henryhsun/TuxTester/04 - Media/Photos & Videos/02 - Progress Documentation/electrical_debug (1).JPG

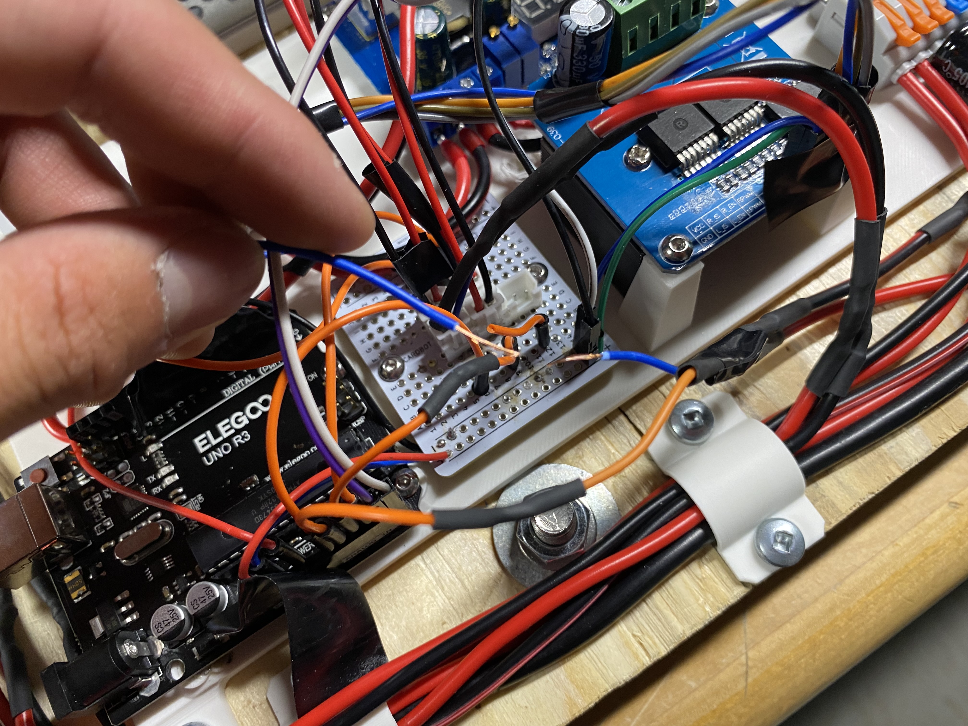
04 - Media/Photos & Videos/02 - Progress Documentation/electrical_debug (1).JPG
