henryhsun/TuxTester/02 - Electrical/Logic_Diagram.png

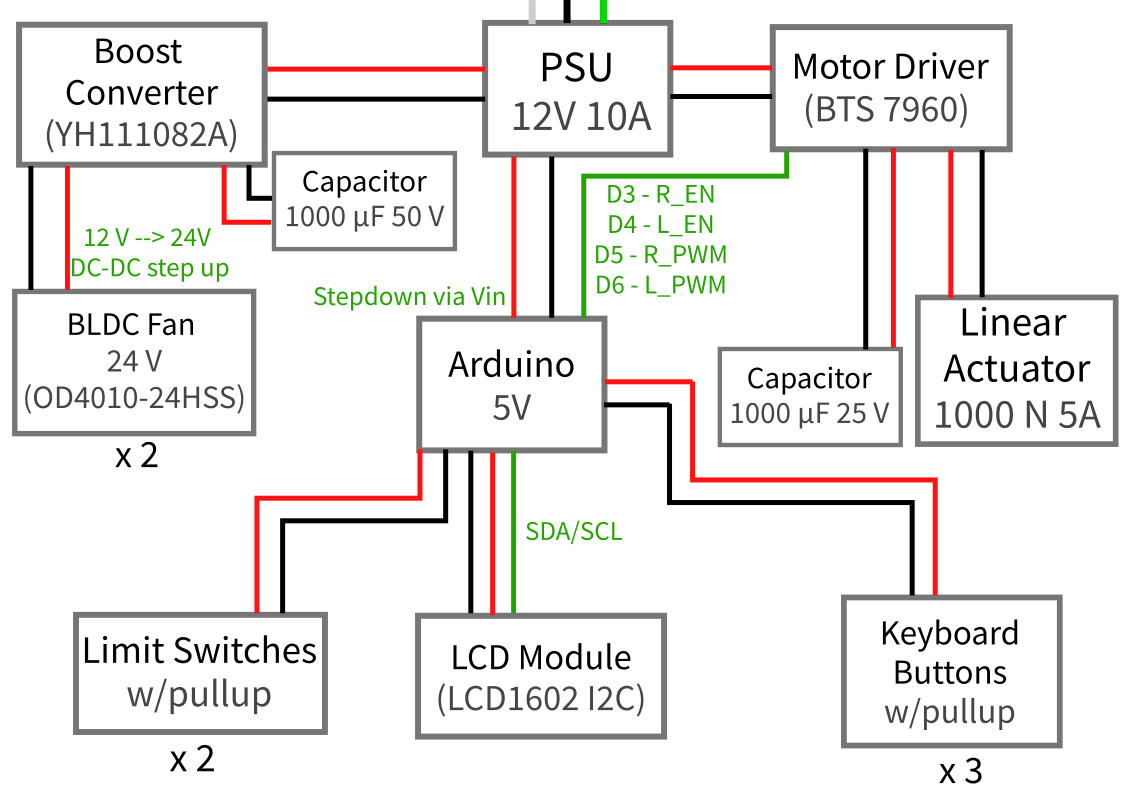
02 - Electrical/Logic_Diagram.png
