henryhsun/TuxTester/02 - Electrical/Schematic Screenshot.png

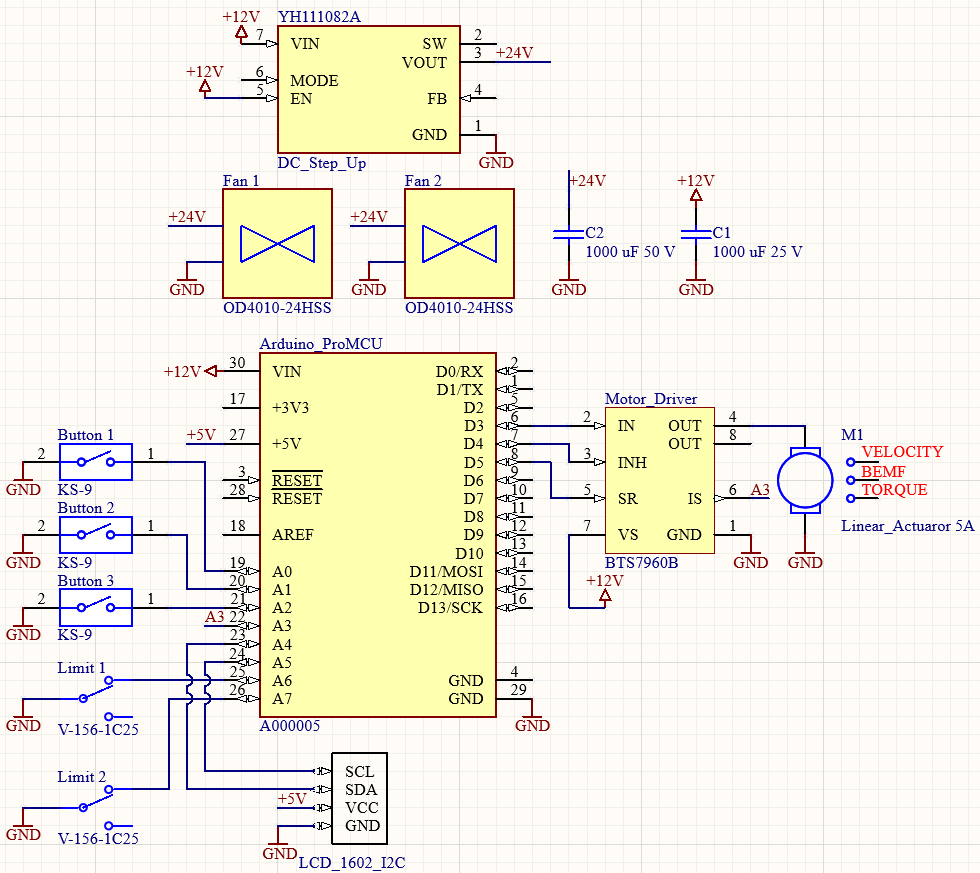
02 - Electrical/Schematic Screenshot.png
