henryhsun/TuxTester/03 - Software/program_flowchart.png

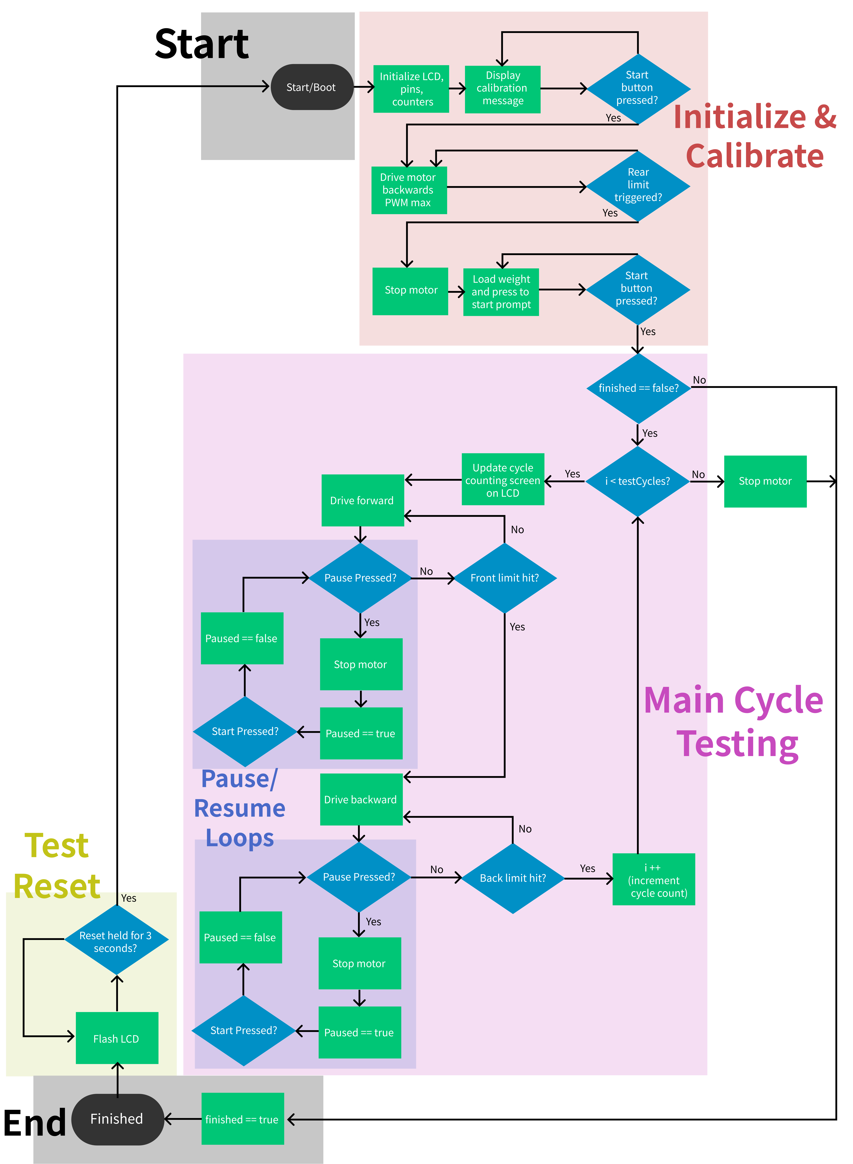
03 - Software/program_flowchart.png
