henryhsun/TuxTester/04 - Media/Photos & Videos/02 - Progress Documentation/CI (5).JPG

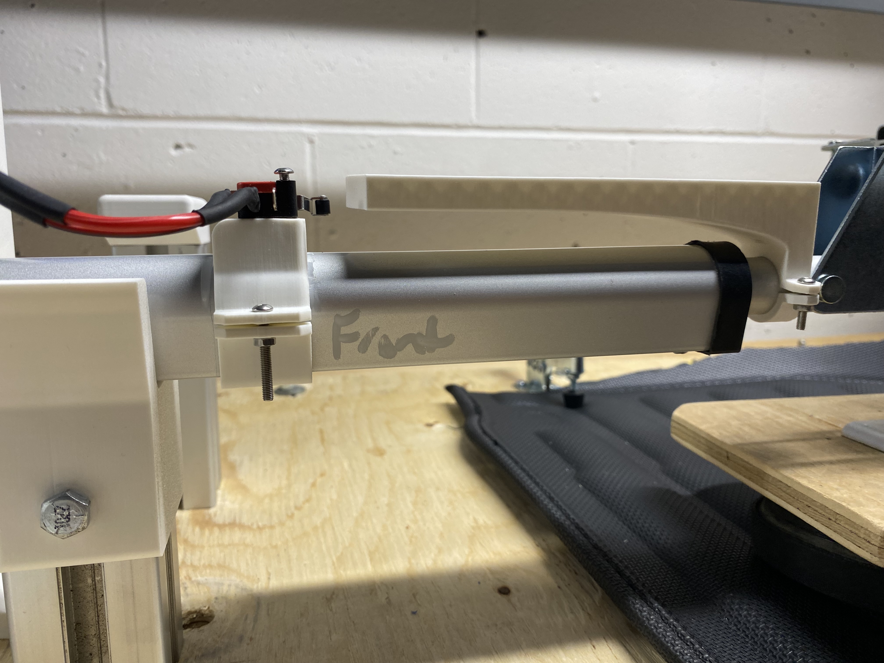
04 - Media/Photos & Videos/02 - Progress Documentation/CI (5).JPG
