henryhsun/TuxTester/04 - Media/Photos & Videos/02 - Progress Documentation/general (8).JPG

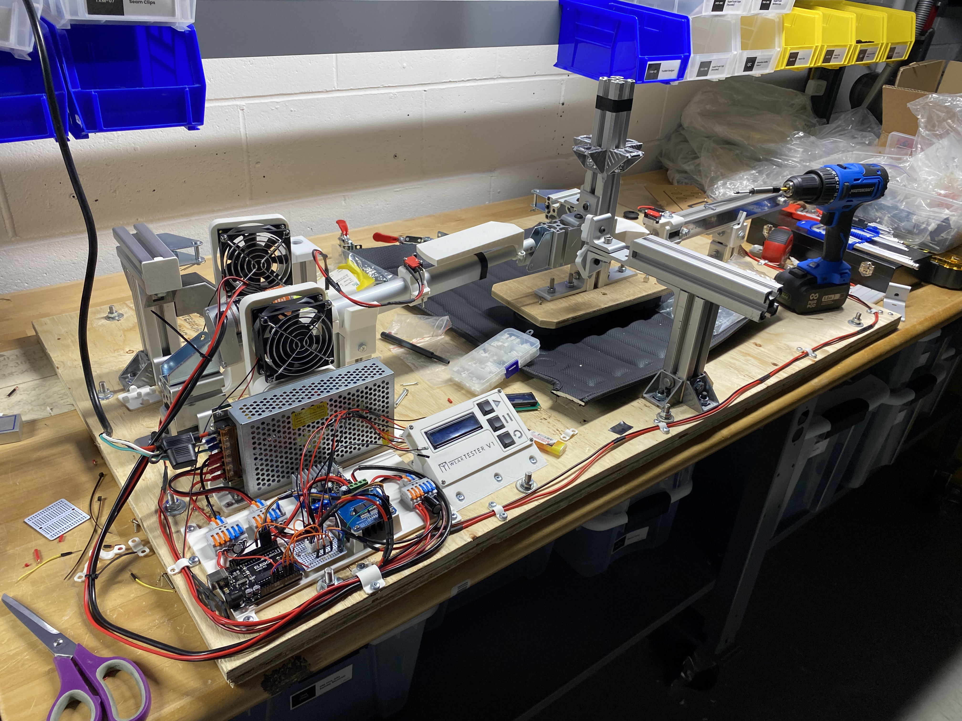
04 - Media/Photos & Videos/02 - Progress Documentation/general (8).JPG
