henryhsun/TuxTester/04 - Media/Photos & Videos/02 - Progress Documentation/limit_switch.JPG

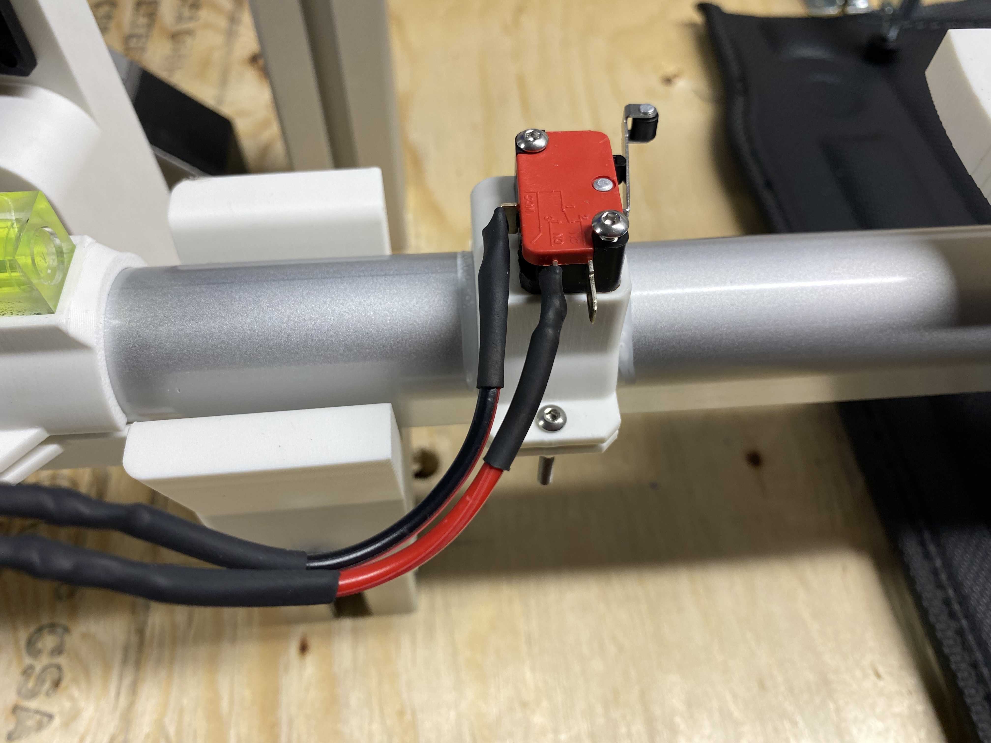
04 - Media/Photos & Videos/02 - Progress Documentation/limit_switch.JPG
