henryhsun/TuxTester/04 - Media/Photos & Videos/02 - Progress Documentation/magnet_holder (1).JPG

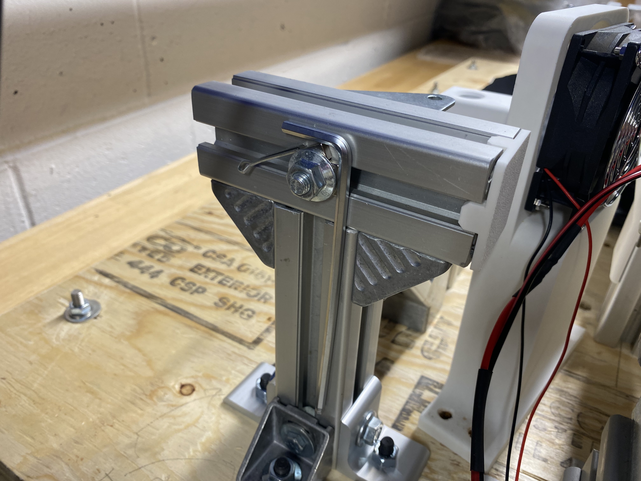
04 - Media/Photos & Videos/02 - Progress Documentation/magnet_holder (1).JPG
