henryhsun/TuxTester/04 - Media/Photos & Videos/03 - Misc/blown_cap.JPG

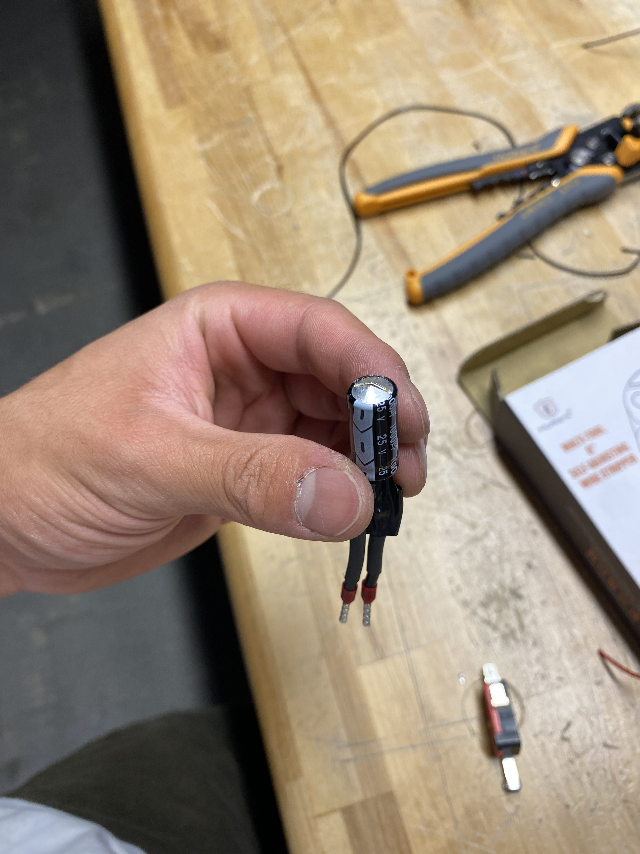
04 - Media/Photos & Videos/03 - Misc/blown_cap.JPG
