henryhsun/TuxTester/04 - Media/Photos & Videos/03 - Misc/broken_snips.JPG

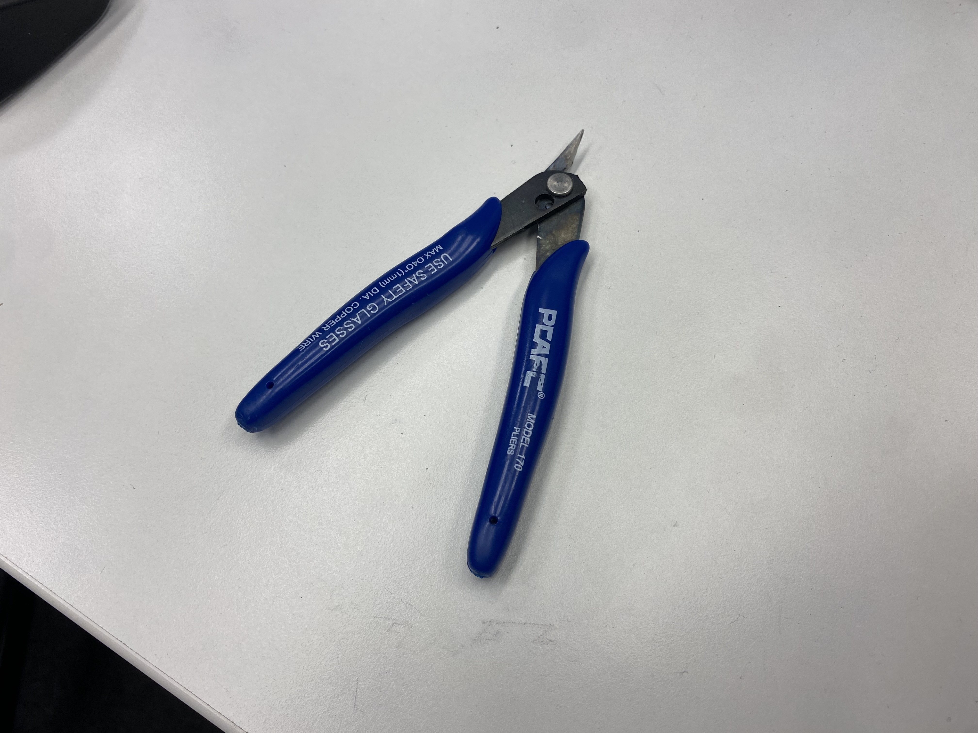
04 - Media/Photos & Videos/03 - Misc/broken_snips.JPG
