henryhsun/TuxTester/04 - Media/Photos & Videos/03 - Misc/cooked_LCD (1).JPG

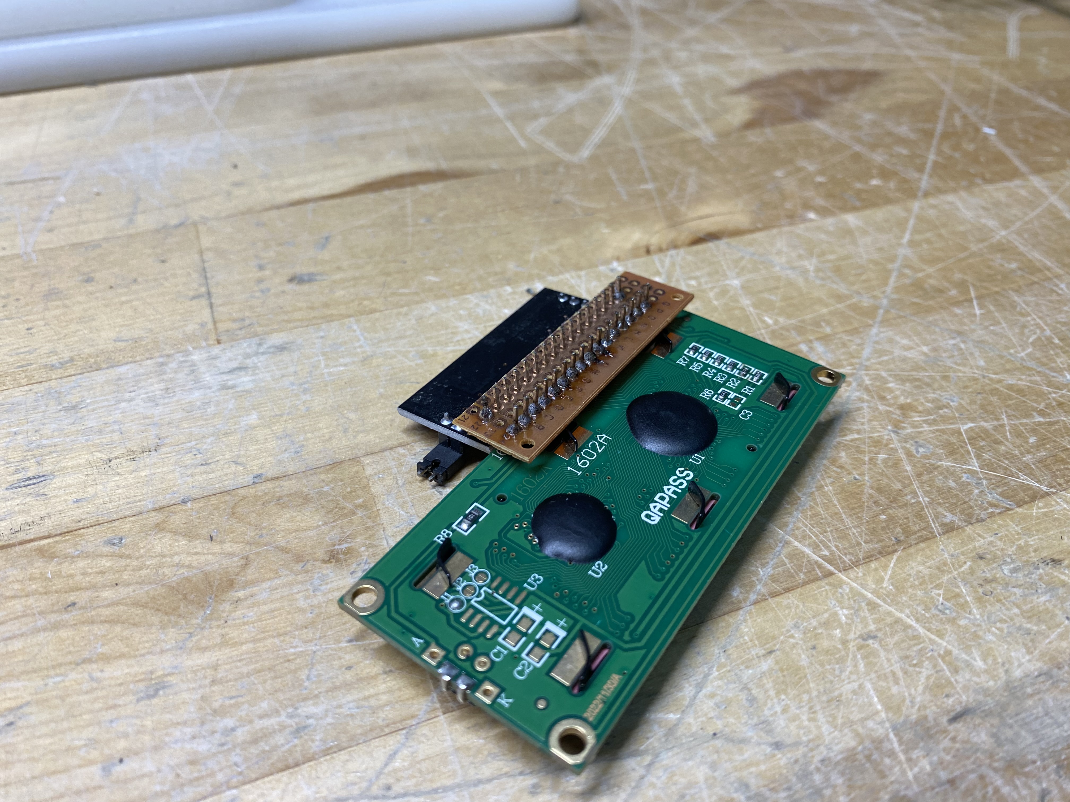
04 - Media/Photos & Videos/03 - Misc/cooked_LCD (1).JPG
