henryhsun/TuxTester/04 - Media/Photos & Videos/03 - Misc/erm/Thread Spray (7).JPG

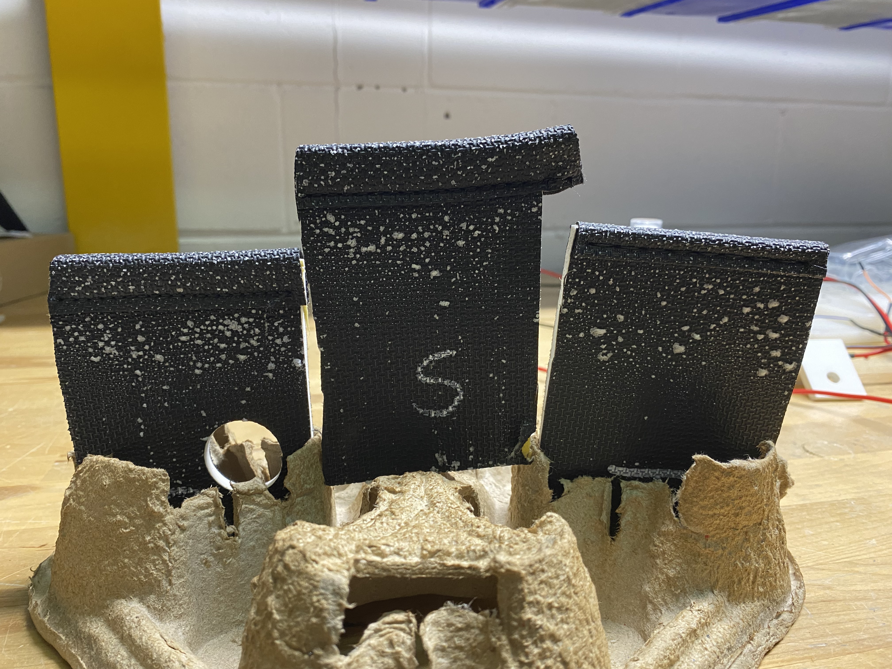
04 - Media/Photos & Videos/03 - Misc/erm/Thread Spray (7).JPG
