henryhsun/TuxTester/04 - Media/Photos & Videos/03 - Misc/erm/Thread Wick (4).JPG

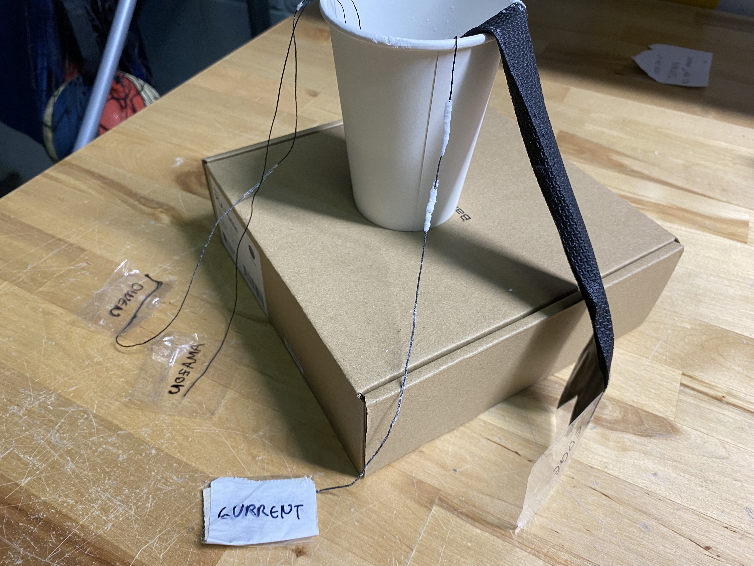
04 - Media/Photos & Videos/03 - Misc/erm/Thread Wick (4).JPG
