henryhsun/TuxTester/04 - Media/Photos & Videos/03 - Misc/erm/Trunk Study (3).JPG

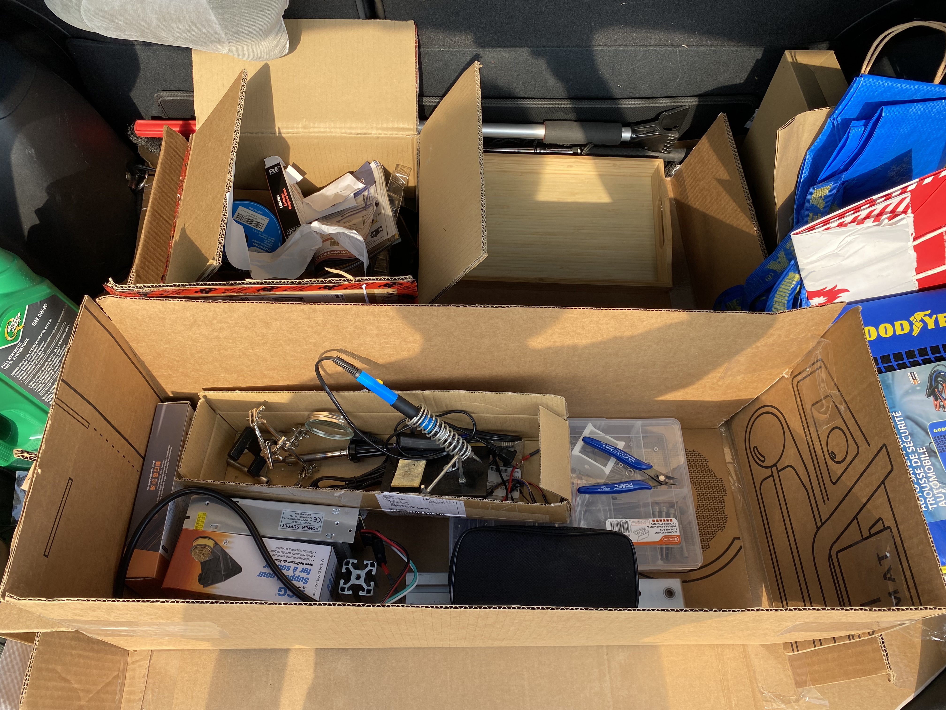
04 - Media/Photos & Videos/03 - Misc/erm/Trunk Study (3).JPG
