henryhsun/TuxTester/01 - Mechanical/CAD/V4 Release 1/Final1Final1PSU_assembly.SLDASM

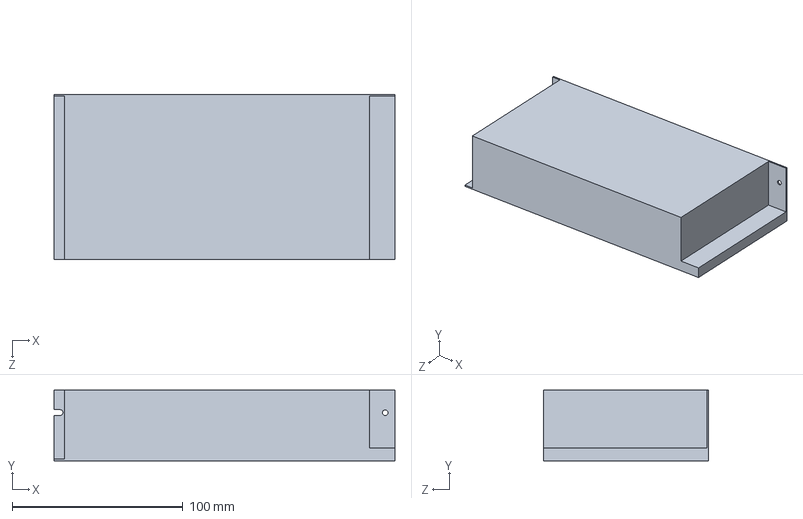
[picture p54: CAD file, 2026-01-19]
01 - Mechanical/CAD/V4 Release 1/Final1Final1PSU_assembly.SLDASM
200.0 x 41.5 x 97.0 mm
