henryhsun/TuxTester/01 - Mechanical/CAD/V3..5 Revised 3D Prints and assembly/STEP/master_extrusion connector.STEP

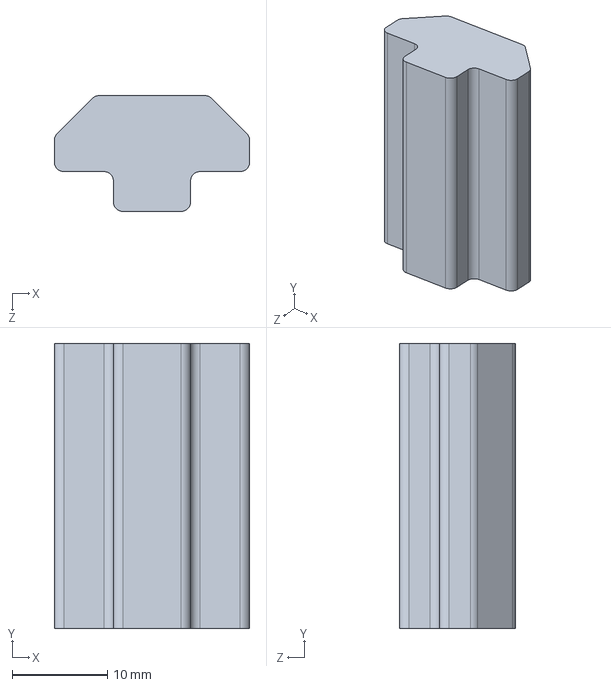
[picture p68: CAD file, 2025-09-29]
01 - Mechanical/CAD/V3..5 Revised 3D Prints and assembly/STEP/master_extrusion connector.STEP
20.6 x 30.0 x 12.2 mm
