henryhsun/TuxTester/01 - Mechanical/CAD/V4 Release 1/Final1masterLevel.SLDPRT

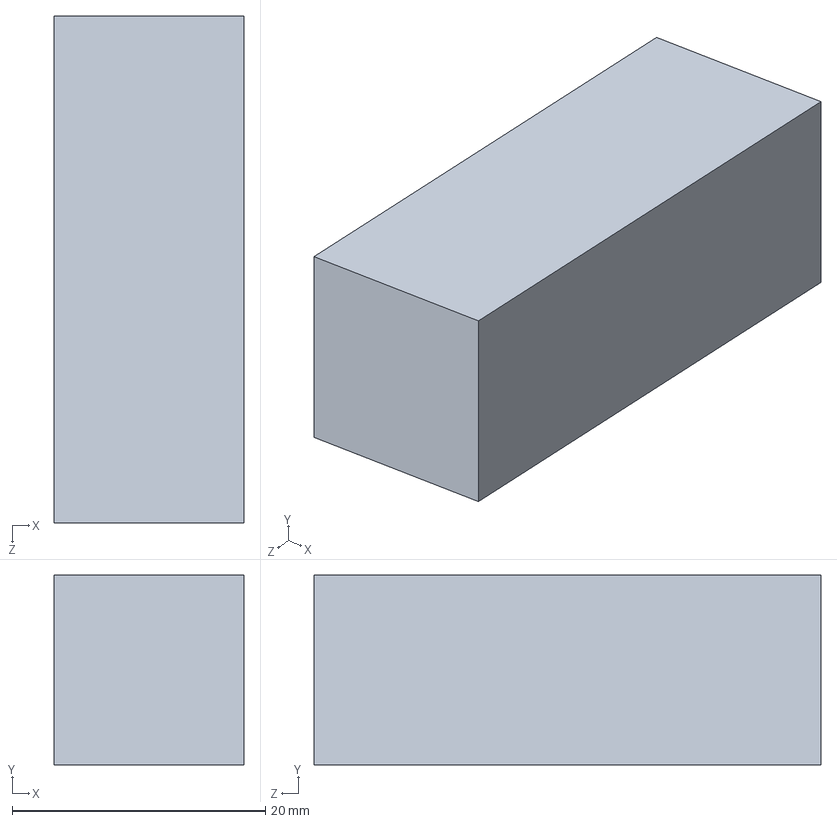
[picture p69: CAD file, 2026-01-19]
01 - Mechanical/CAD/V4 Release 1/Final1masterLevel.SLDPRT
15.0 x 15.0 x 40.0 mm
