henryhsun/TuxTester/01 - Mechanical/CAD/V3..5 Revised 3D Prints and assembly/STEP/master_Hinge_Bushing3.STEP

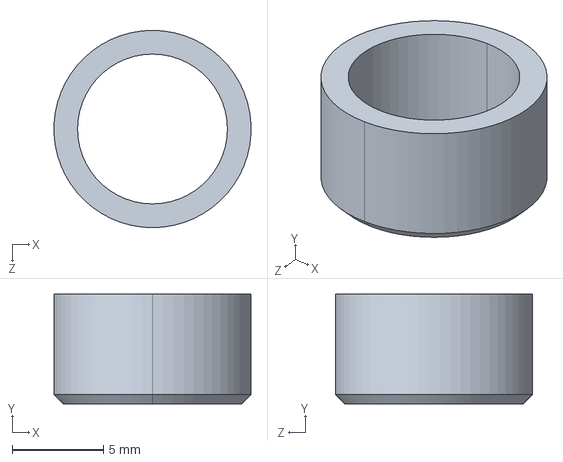
[picture p70: CAD file, 2025-09-29]
01 - Mechanical/CAD/V3..5 Revised 3D Prints and assembly/STEP/master_Hinge_Bushing3.STEP
10.8 x 6.00 x 10.8 mm
