henryhsun/TuxTester/01 - Mechanical/CAD/V3..5 Revised 3D Prints and assembly/STEP/master_Sole Spacer.STEP

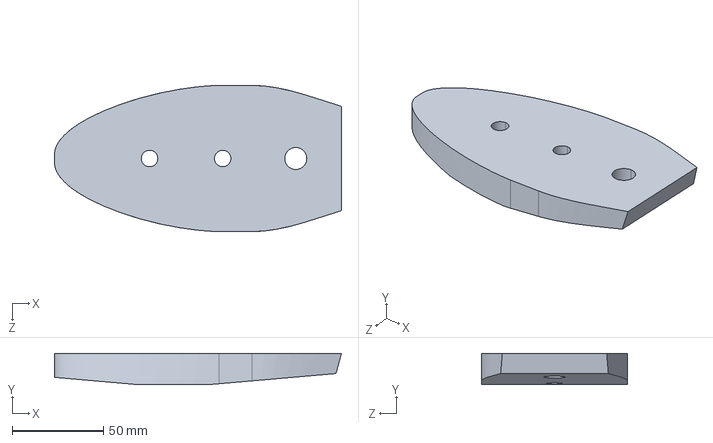
[picture p71: CAD file, 2025-09-29]
01 - Mechanical/CAD/V3..5 Revised 3D Prints and assembly/STEP/master_Sole Spacer.STEP
157.0 x 17.0 x 80.0 mm
