henryhsun/TuxTester/01 - Mechanical/CAD/V4 Release 1/Final1masterRuler.SLDPRT

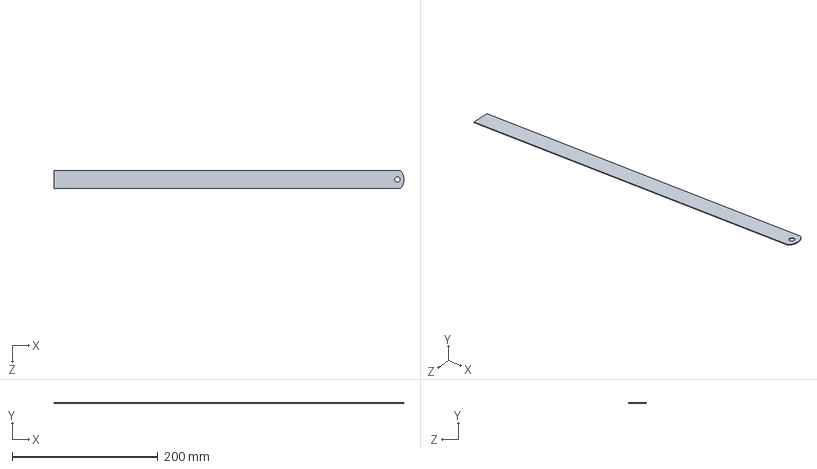
[picture p72: CAD file, 2026-01-19]
01 - Mechanical/CAD/V4 Release 1/Final1masterRuler.SLDPRT
479.9 x 0.9 x 25.1 mm
