henryhsun/TuxTester/01 - Mechanical/CAD/V3..5 Revised 3D Prints and assembly/STEP/master_rulerPointer.STEP

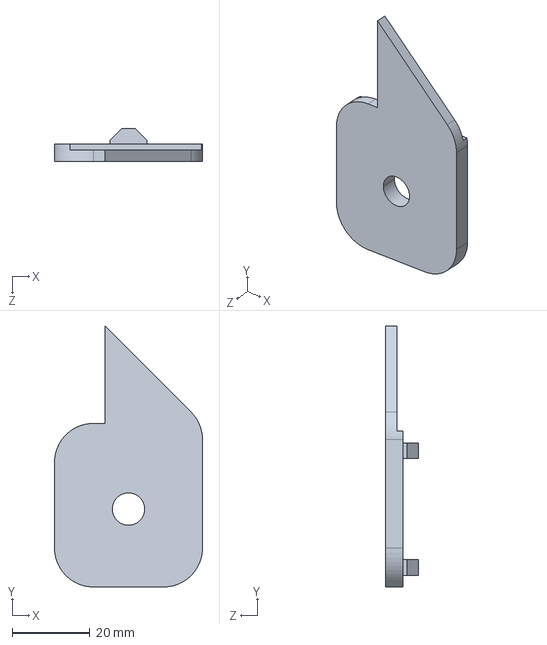
[picture p73: CAD file, 2025-09-29]
01 - Mechanical/CAD/V3..5 Revised 3D Prints and assembly/STEP/master_rulerPointer.STEP
38.0 x 67.0 x 8.50 mm
