henryhsun/TuxTester/01 - Mechanical/CAD/V3..5 Revised 3D Prints and assembly/STEP/masterSwitch_Mount.STEP

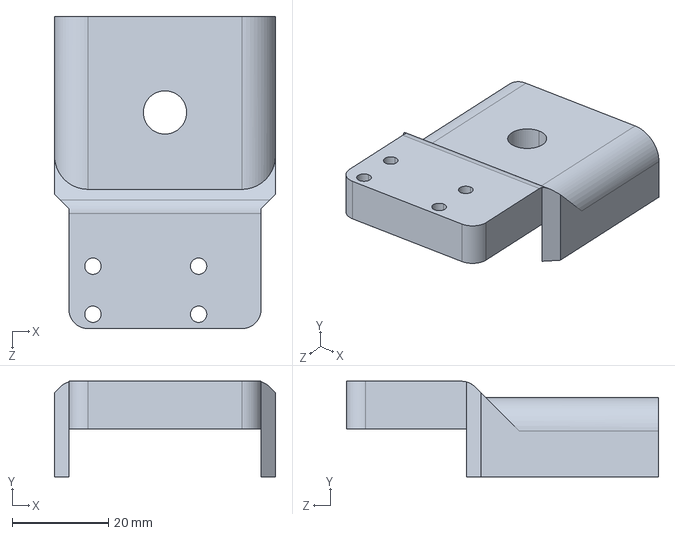
[picture p75: CAD file, 2025-09-29]
01 - Mechanical/CAD/V3..5 Revised 3D Prints and assembly/STEP/masterSwitch_Mount.STEP
46.0 x 19.9 x 65.0 mm
