henryhsun/TuxTester/01 - Mechanical/CAD/V3..5 Revised 3D Prints and assembly/STEP/master_Hinge_Spacer.STEP

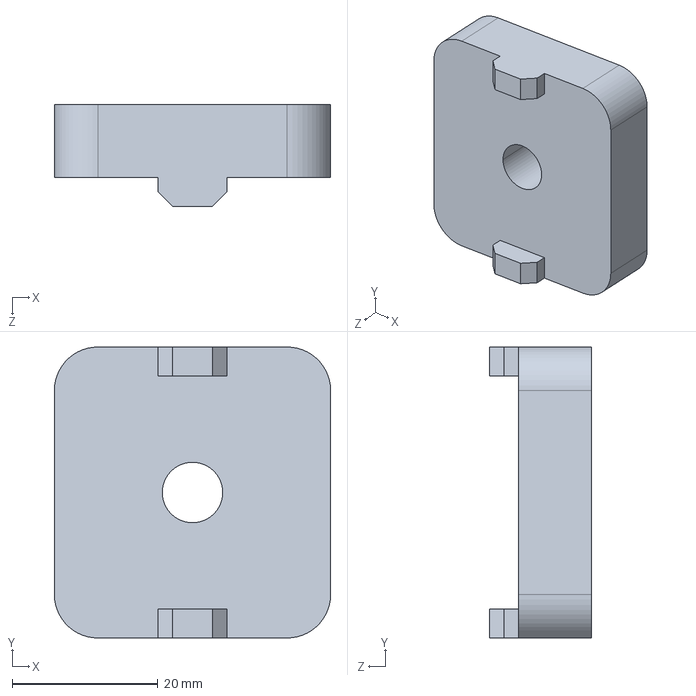
[picture p77: CAD file, 2025-09-29]
01 - Mechanical/CAD/V3..5 Revised 3D Prints and assembly/STEP/master_Hinge_Spacer.STEP
38.0 x 40.0 x 14.0 mm
