henryhsun/TuxTester/01 - Mechanical/CAD/V4 Release 1/Final1masterRivet - long.SLDPRT

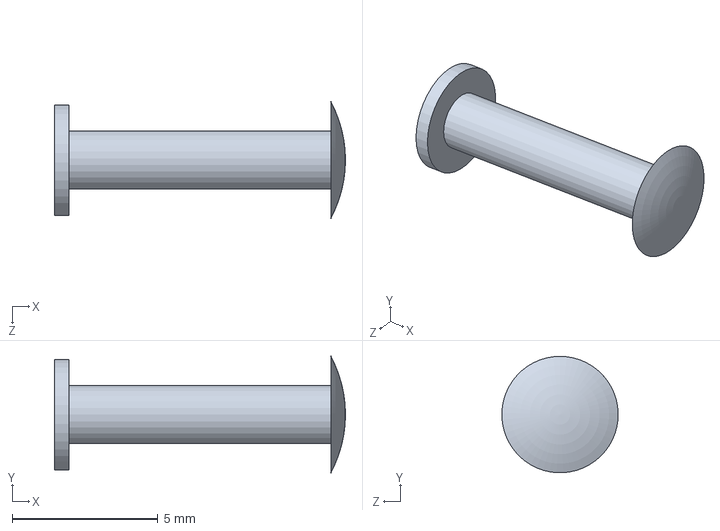
[picture p78: CAD file, 2026-01-19]
01 - Mechanical/CAD/V4 Release 1/Final1masterRivet - long.SLDPRT
10.0 x 4.00 x 4.00 mm
