henryhsun/TuxTester/01 - Mechanical/CAD/V3..5 Revised 3D Prints and assembly/STEP/masterSwitch_Actuator_Mount.STEP

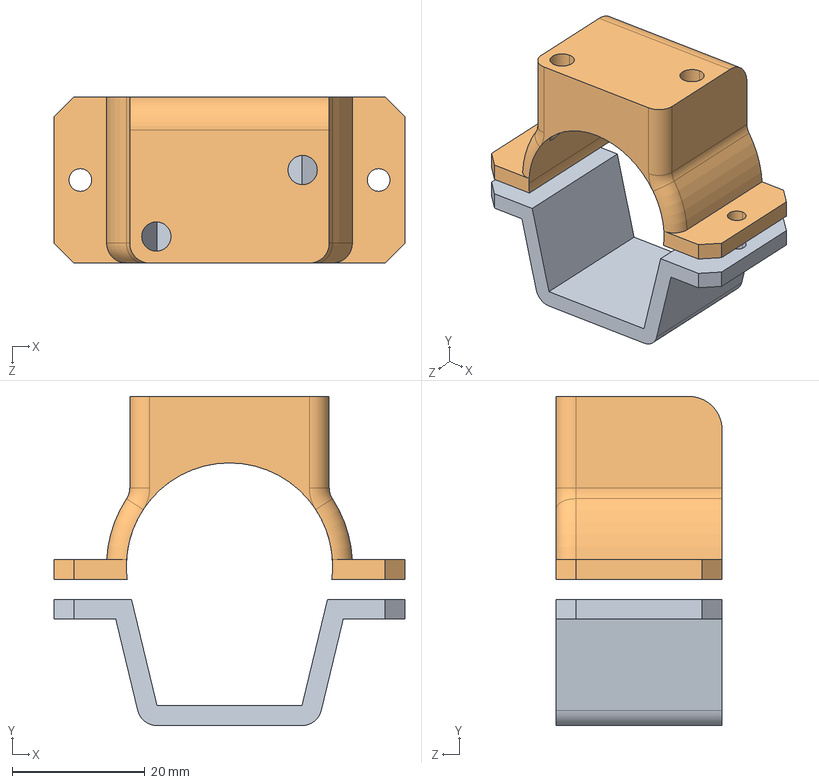
[picture p79: CAD file, 2025-09-29]
01 - Mechanical/CAD/V3..5 Revised 3D Prints and assembly/STEP/masterSwitch_Actuator_Mount.STEP
52.8 x 49.5 x 25.0 mm
