henryhsun/TuxTester/01 - Mechanical/CAD/V3..5 Revised 3D Prints and assembly/STEP/master_actuatorHolder1.STEP

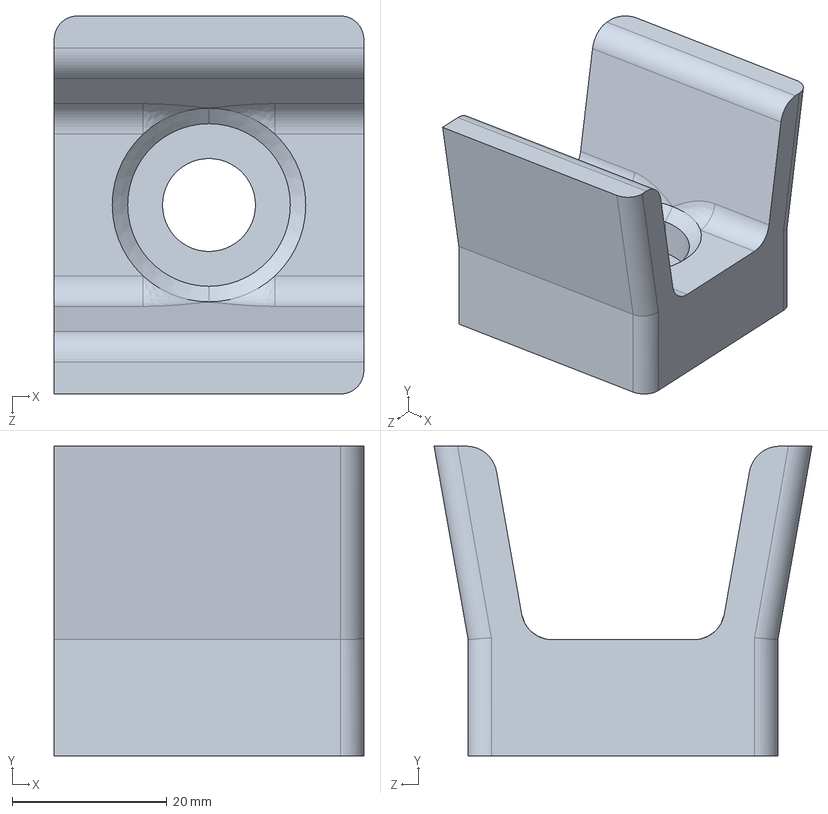
[picture p80: CAD file, 2025-09-29]
01 - Mechanical/CAD/V3..5 Revised 3D Prints and assembly/STEP/master_actuatorHolder1.STEP
40.0 x 40.0 x 48.8 mm
