henryhsun/TuxTester/01 - Mechanical/CAD/V4 Release 1/Final1masterShaft_Clamp_Striker.SLDPRT

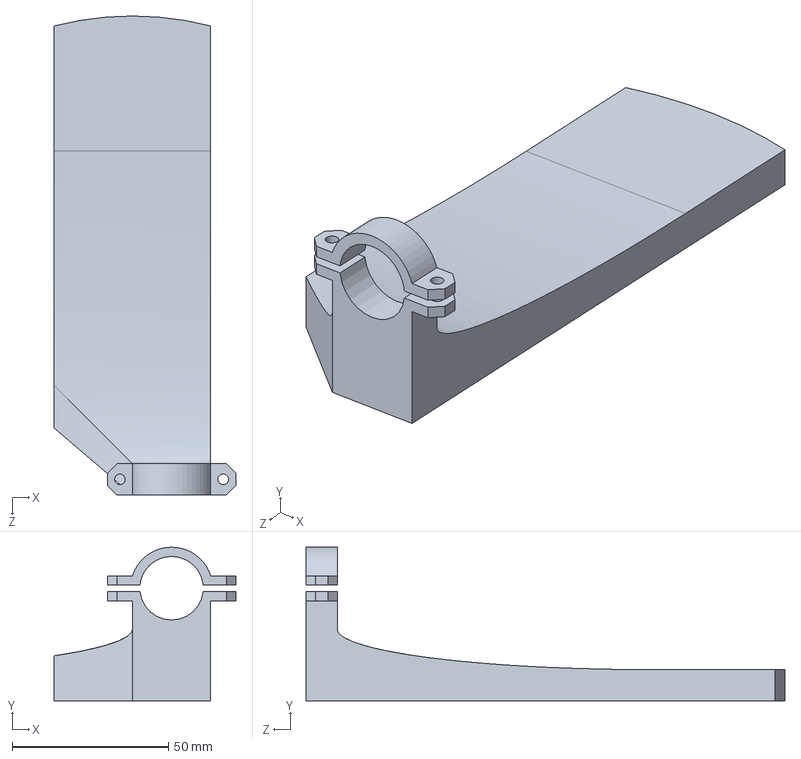
[picture p81: CAD file, 2026-01-19]
01 - Mechanical/CAD/V4 Release 1/Final1masterShaft_Clamp_Striker.SLDPRT
58.1 x 49.1 x 153.2 mm
