henryhsun/TuxTester/01 - Mechanical/CAD/V4 Release 1/Final1masterArm.SLDPRT

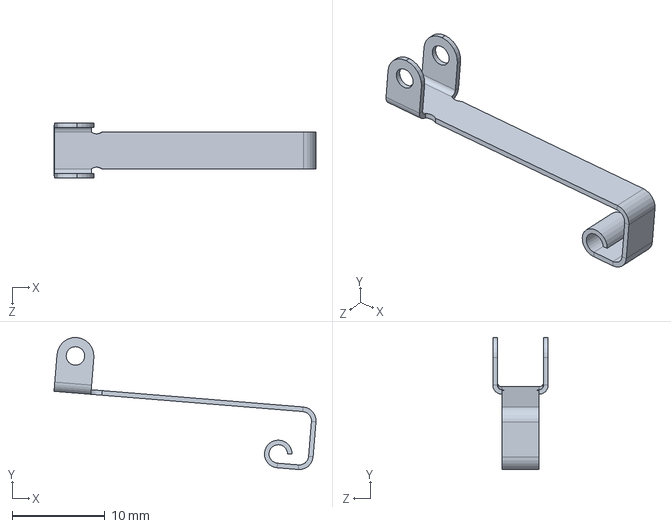
[picture p82: CAD file, 2026-01-19]
01 - Mechanical/CAD/V4 Release 1/Final1masterArm.SLDPRT
28.3 x 14.3 x 6.00 mm
