henryhsun/TuxTester/01 - Mechanical/CAD/V4 Release 1/Final1masterActuator_Body.SLDPRT

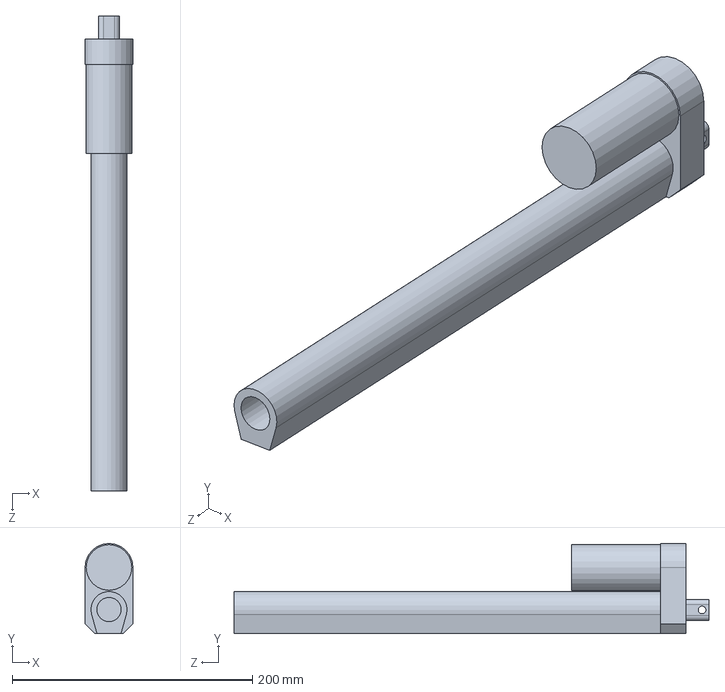
[picture p83: CAD file, 2026-01-19]
01 - Mechanical/CAD/V4 Release 1/Final1masterActuator_Body.SLDPRT
40.0 x 75.0 x 395.2 mm
