henryhsun/TuxTester/01 - Mechanical/CAD/V4 Release 1/Final1master4040_2HoleBracket.SLDPRT

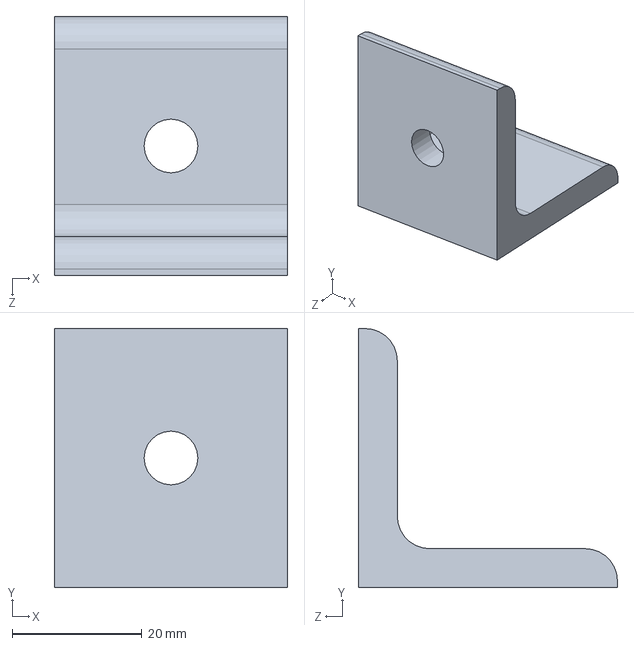
[picture p85: CAD file, 2026-01-19]
01 - Mechanical/CAD/V4 Release 1/Final1master4040_2HoleBracket.SLDPRT
36.0 x 40.0 x 40.0 mm
