henryhsun/TuxTester/01 - Mechanical/CAD/V4 Release 1/Final1Final1fan holderSHORT.SLDPRT

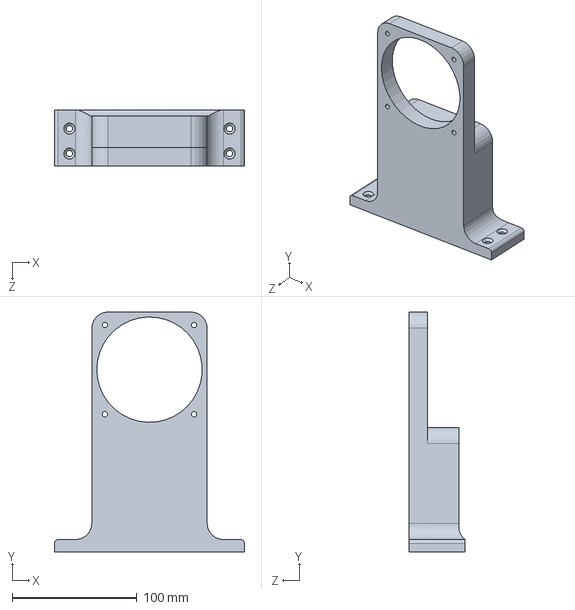
[picture p86: CAD file, 2026-01-19]
01 - Mechanical/CAD/V4 Release 1/Final1Final1fan holderSHORT.SLDPRT
152.5 x 192.5 x 45.0 mm
