henryhsun/TuxTester/01 - Mechanical/CAD/V4 Release 1/Final1masterBody.SLDPRT

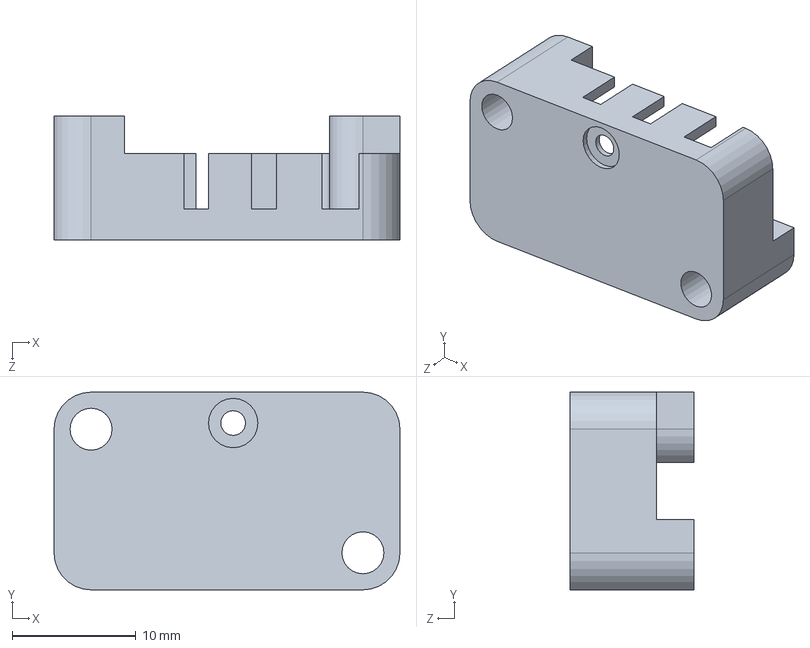
[picture p87: CAD file, 2026-01-19]
01 - Mechanical/CAD/V4 Release 1/Final1masterBody.SLDPRT
28.0 x 16.0 x 10.0 mm
