henryhsun/TuxTester/01 - Mechanical/CAD/V4 Release 1/Final1masterActuator_Shaft.SLDPRT

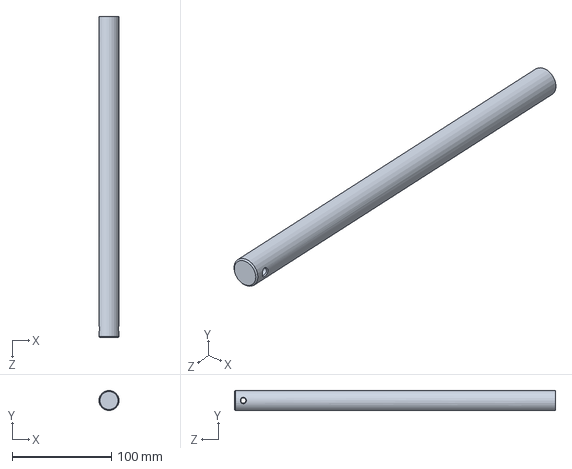
[picture p88: CAD file, 2026-01-19]
01 - Mechanical/CAD/V4 Release 1/Final1masterActuator_Shaft.SLDPRT
20.2 x 20.2 x 323.3 mm
