henryhsun/TuxTester/01 - Mechanical/CAD/V4 Release 1/Final1master4040 x 45.4.SLDPRT

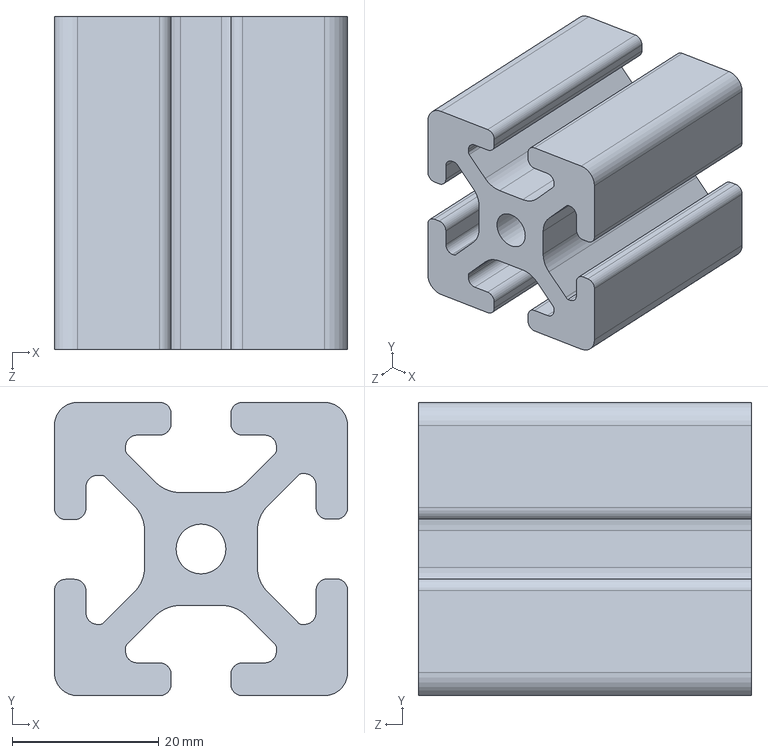
[picture p89: CAD file, 2026-01-19]
01 - Mechanical/CAD/V4 Release 1/Final1master4040 x 45.4.SLDPRT
40.0 x 40.0 x 45.4 mm
