henryhsun/TuxTester/01 - Mechanical/CAD/V4 Release 1/Final1masterActuator_Pin.SLDPRT

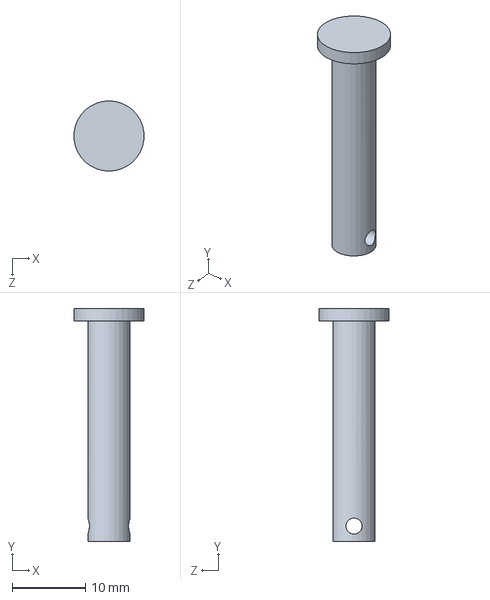
[picture p90: CAD file, 2026-01-19]
01 - Mechanical/CAD/V4 Release 1/Final1masterActuator_Pin.SLDPRT
9.56 x 31.9 x 9.60 mm
