henryhsun/TuxTester/01 - Mechanical/CAD/V4 Release 1/Final1masterSwitch_Mount.SLDPRT

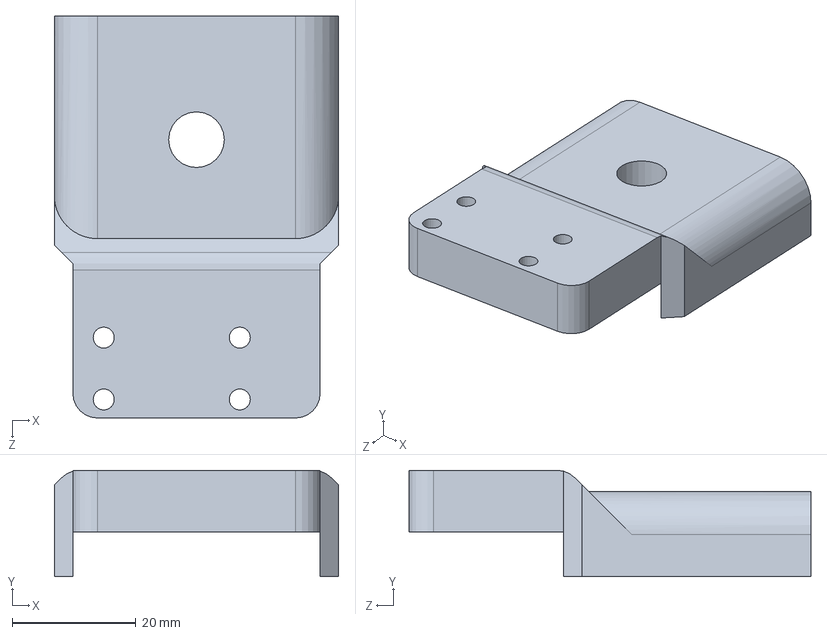
[picture p92: CAD file, 2026-01-19]
01 - Mechanical/CAD/V4 Release 1/Final1masterSwitch_Mount.SLDPRT
46.0 x 17.2 x 65.0 mm
