henryhsun/TuxTester/01 - Mechanical/CAD/V4 Release 1/Final1Final1console.SLDPRT

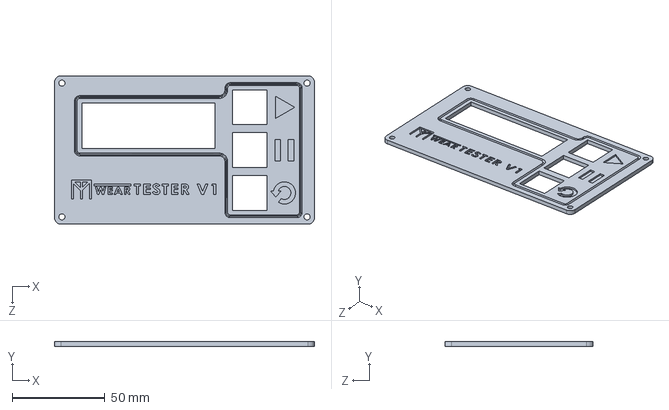
[picture p93: CAD file, 2026-01-19]
01 - Mechanical/CAD/V4 Release 1/Final1Final1console.SLDPRT
140.1 x 2.50 x 80.0 mm
