henryhsun/TuxTester/01 - Mechanical/CAD/V4 Release 1/Final1Final1fan holderTALL.SLDPRT

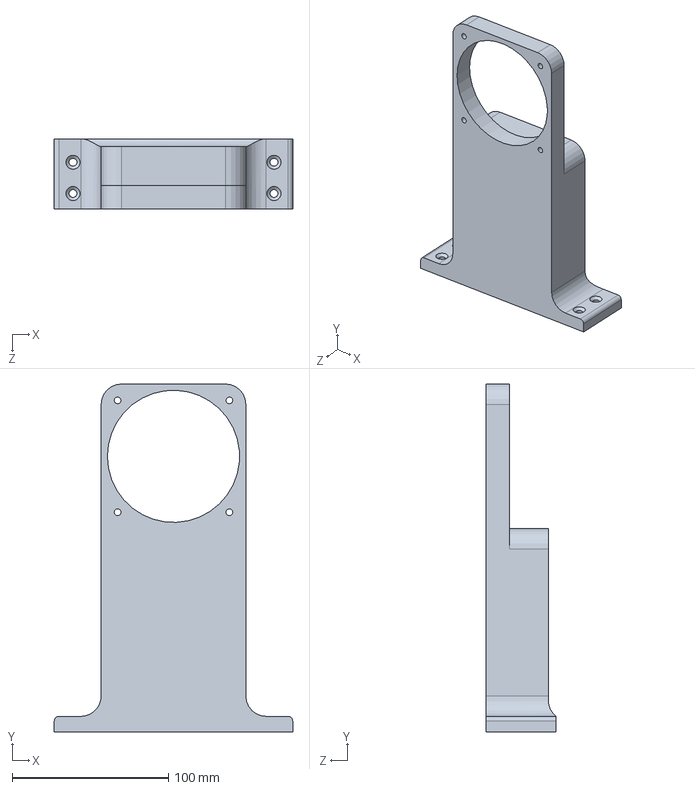
[picture p94: CAD file, 2026-01-19]
01 - Mechanical/CAD/V4 Release 1/Final1Final1fan holderTALL.SLDPRT
152.5 x 222.5 x 45.0 mm
