henryhsun/TuxTester/01 - Mechanical/CAD/V4 Release 1/Final1master4040 x 85.4.SLDPRT

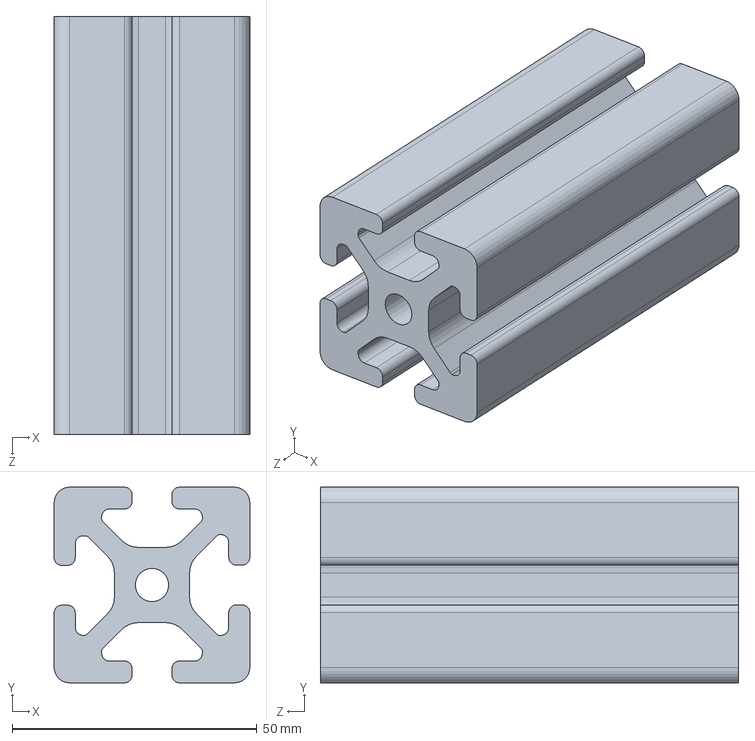
[picture p95: CAD file, 2026-01-19]
01 - Mechanical/CAD/V4 Release 1/Final1master4040 x 85.4.SLDPRT
40.0 x 40.0 x 85.4 mm
