henryhsun/TuxTester/01 - Mechanical/CAD/V4 Release 1/Final1masterSwitch_Actuator_Mount.SLDPRT

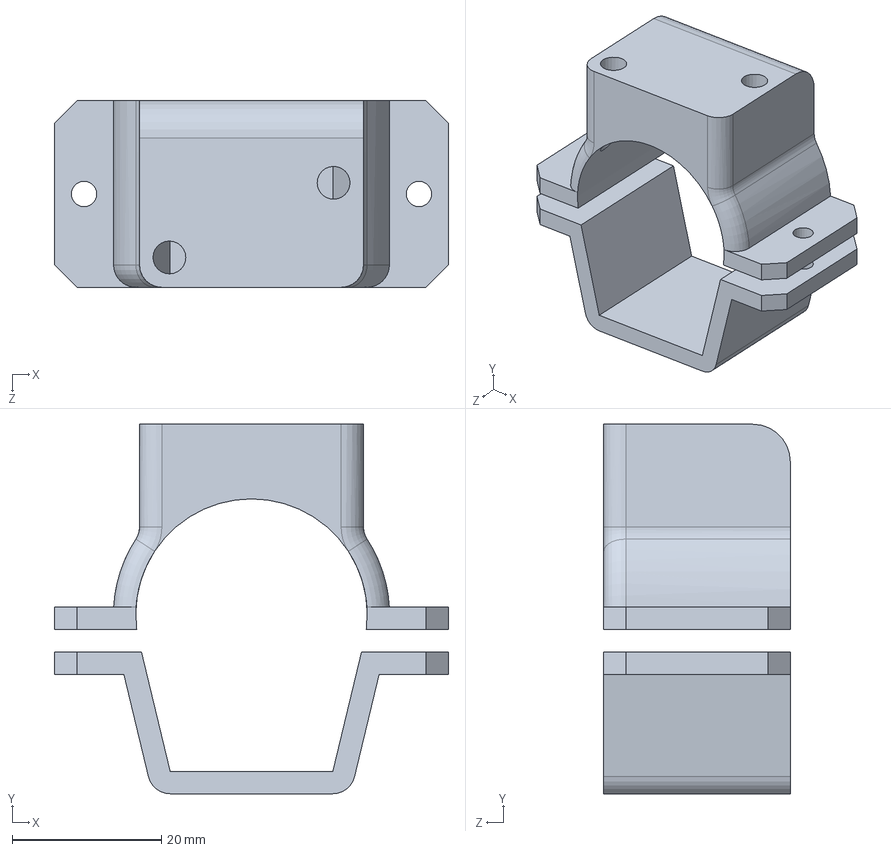
[picture p96: CAD file, 2026-01-19]
01 - Mechanical/CAD/V4 Release 1/Final1masterSwitch_Actuator_Mount.SLDPRT
52.8 x 49.5 x 25.0 mm
