henryhsun/TuxTester/01 - Mechanical/CAD/V4 Release 1/Final1master5128A22_Low-Profile Hold-Down Toggle Clamp.SLDPRT

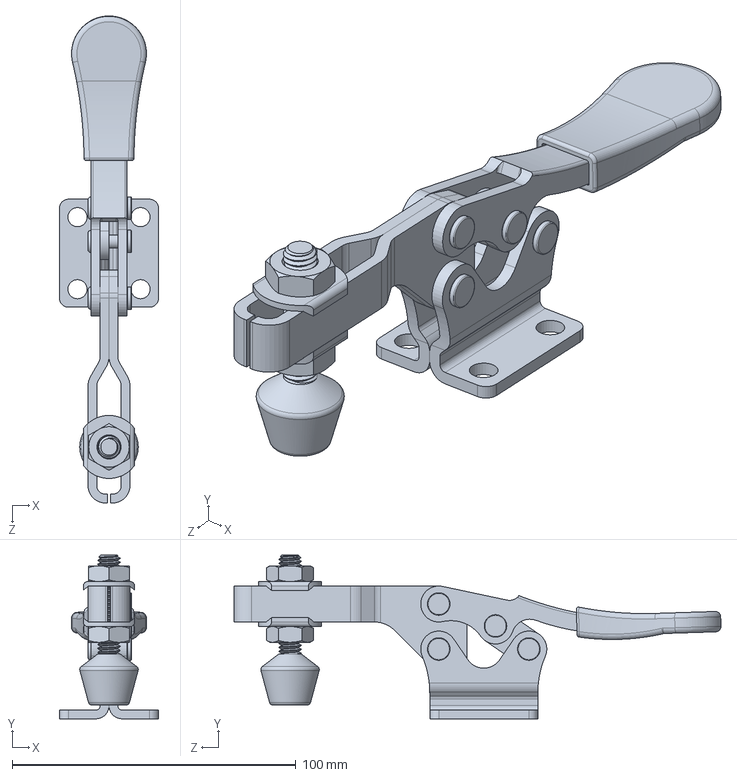
[picture p97: CAD file, 2026-01-19]
01 - Mechanical/CAD/V4 Release 1/Final1master5128A22_Low-Profile Hold-Down Toggle Clamp.SLDPRT
34.9 x 57.7 x 171.7 mm
