henryhsun/TuxTester/01 - Mechanical/CAD/V4 Release 1/Final1masterActuator_Bracket.SLDPRT

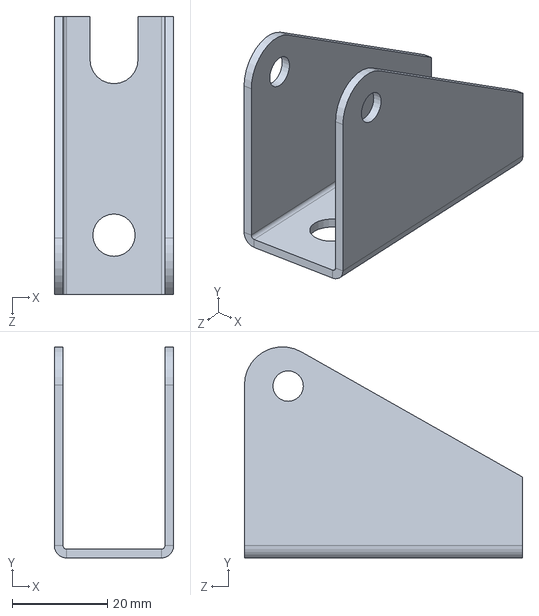
[picture p98: CAD file, 2026-01-19]
01 - Mechanical/CAD/V4 Release 1/Final1masterActuator_Bracket.SLDPRT
25.1 x 44.4 x 58.5 mm
