henryhsun/TuxTester/01 - Mechanical/CAD/V4 Release 1/Final1masterRivet - short.SLDPRT

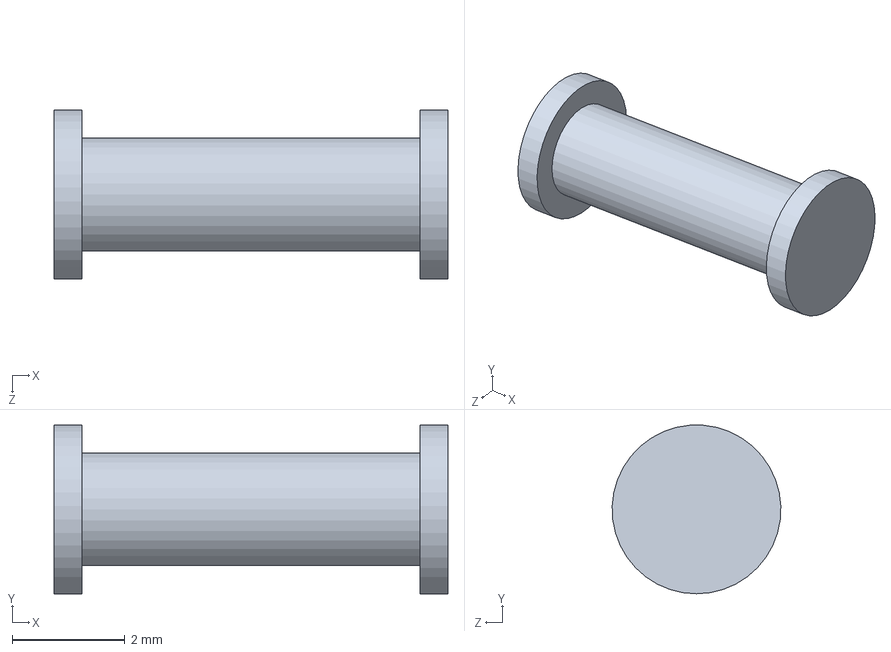
[picture p99: CAD file, 2026-01-19]
01 - Mechanical/CAD/V4 Release 1/Final1masterRivet - short.SLDPRT
7.00 x 3.00 x 3.00 mm
