henryhsun/TuxTester/01 - Mechanical/CAD/V4 Release 1/Final1masterRoll.SLDPRT

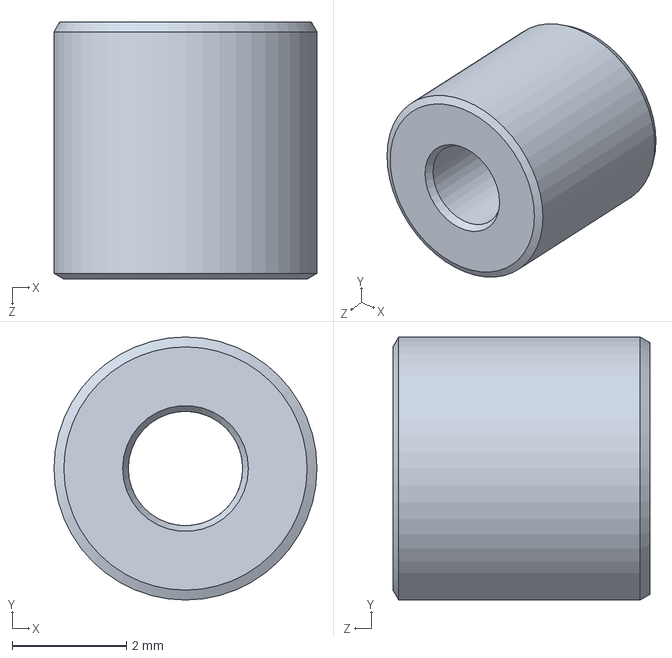
[picture p100: CAD file, 2026-01-19]
01 - Mechanical/CAD/V4 Release 1/Final1masterRoll.SLDPRT
4.60 x 4.60 x 4.50 mm
