henryhsun/TuxTester/01 - Mechanical/CAD/V4 Release 1/Final1masterConnector - bent.SLDPRT

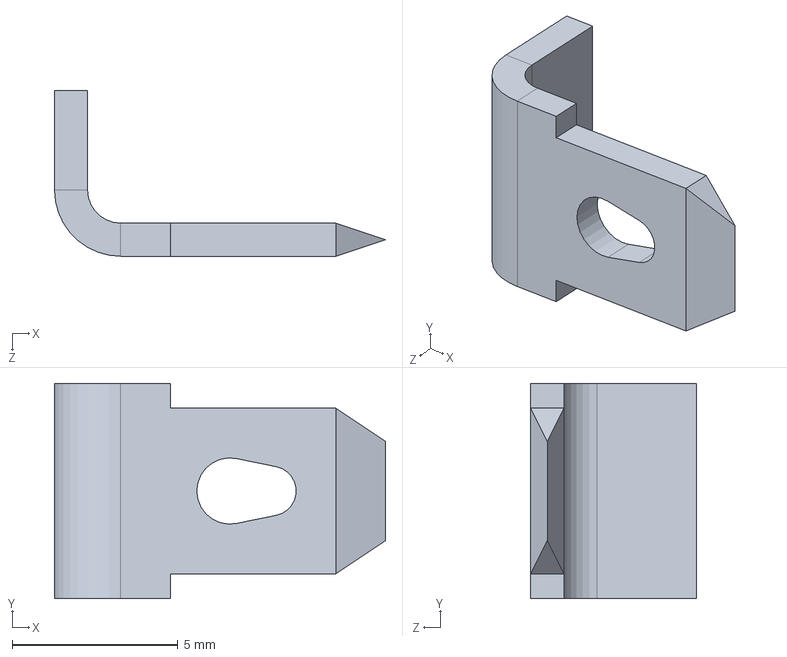
[picture p101: CAD file, 2026-01-19]
01 - Mechanical/CAD/V4 Release 1/Final1masterConnector - bent.SLDPRT
10.0 x 6.50 x 5.00 mm
