henryhsun/TuxTester/01 - Mechanical/CAD/V4 Release 1/Final1master4080 x 60.SLDPRT

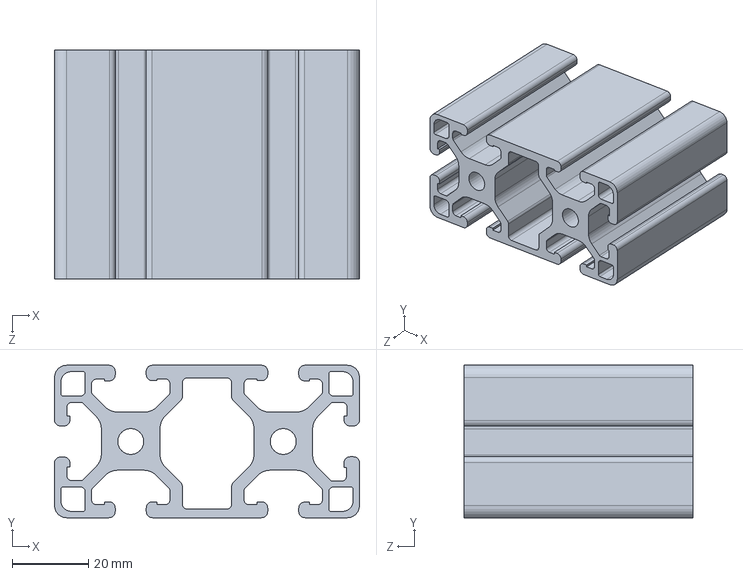
[picture p102: CAD file, 2026-01-19]
01 - Mechanical/CAD/V4 Release 1/Final1master4080 x 60.SLDPRT
80.0 x 40.0 x 60.0 mm
