henryhsun/TuxTester/01 - Mechanical/CAD/V4 Release 1/Final1masterSwitch.SLDPRT

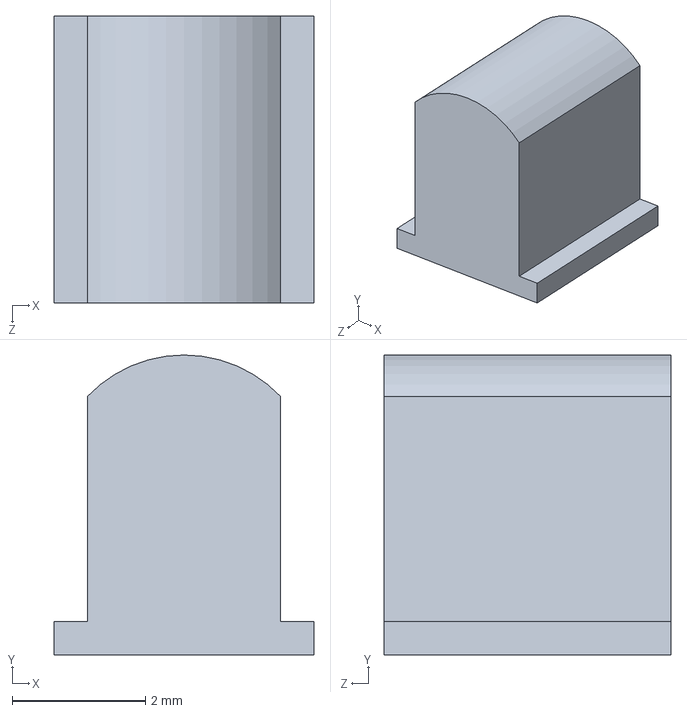
[picture p103: CAD file, 2026-01-19]
01 - Mechanical/CAD/V4 Release 1/Final1masterSwitch.SLDPRT
3.90 x 4.50 x 4.30 mm
