henryhsun/TuxTester/01 - Mechanical/CAD/V4 Release 1/Final1Final1rulerAligner.SLDPRT

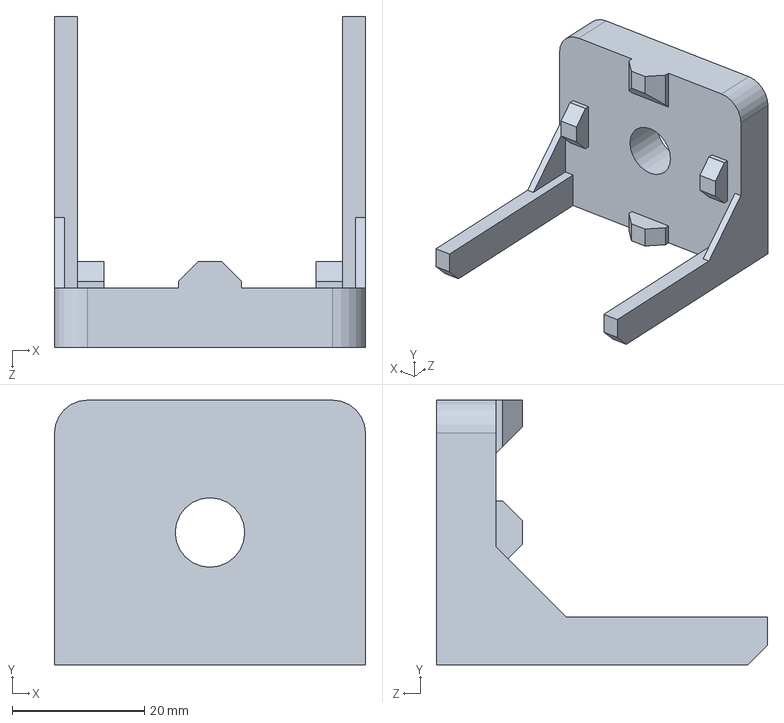
[picture p104: CAD file, 2026-01-19]
01 - Mechanical/CAD/V4 Release 1/Final1Final1rulerAligner.SLDPRT
47.0 x 40.0 x 50.0 mm
