henryhsun/TuxTester/01 - Mechanical/CAD/V4 Release 1/Final1Final1actuatorHolder1.SLDPRT

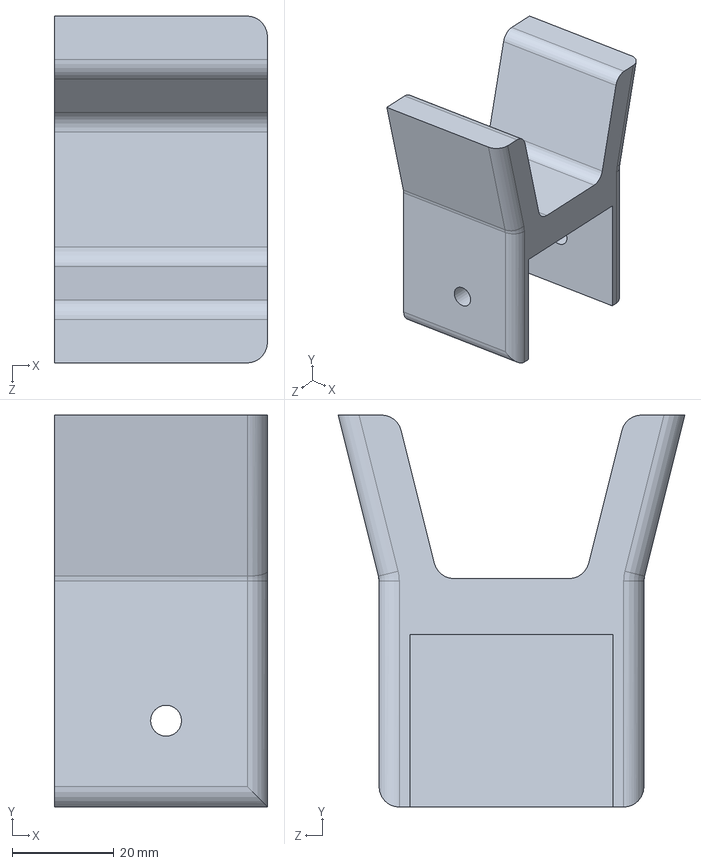
[picture p105: CAD file, 2026-01-19]
01 - Mechanical/CAD/V4 Release 1/Final1Final1actuatorHolder1.SLDPRT
42.0 x 77.2 x 68.3 mm
