henryhsun/TuxTester/01 - Mechanical/CAD/V4 Release 1/Final1Component Board.SLDPRT

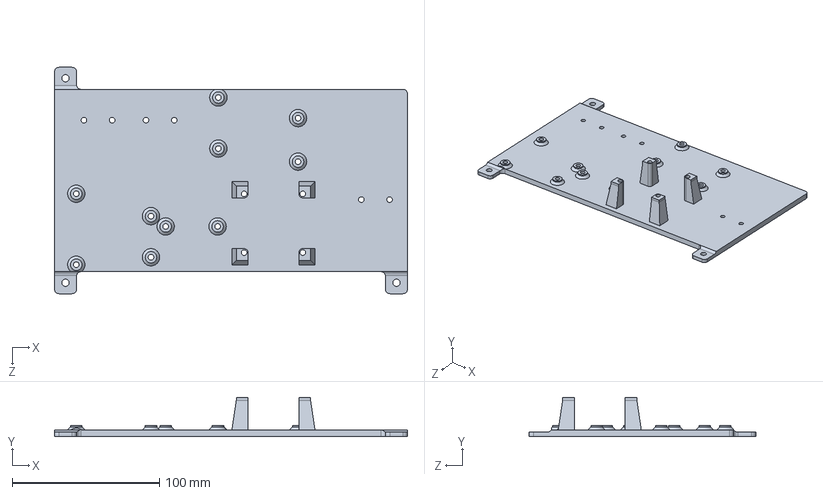
[picture p106: CAD file, 2026-01-19]
01 - Mechanical/CAD/V4 Release 1/Final1Component Board.SLDPRT
240.0 x 26.6 x 154.0 mm
