henryhsun/TuxTester/01 - Mechanical/CAD/V4 Release 1/Final1masterLevel Mount.SLDPRT

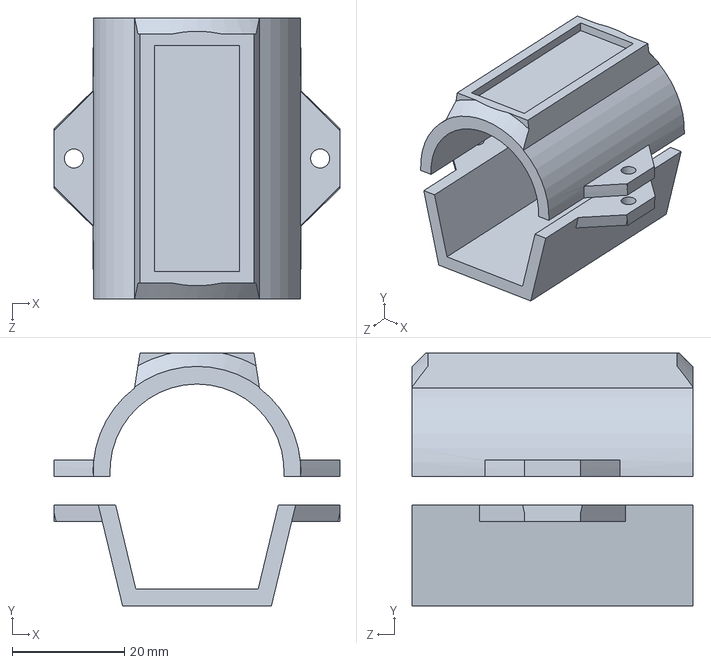
[picture p108: CAD file, 2026-01-19]
01 - Mechanical/CAD/V4 Release 1/Final1masterLevel Mount.SLDPRT
50.9 x 45.0 x 50.0 mm
