henryhsun/TuxTester/01 - Mechanical/CAD/V4 Release 1/Final1masterBase1.SLDPRT

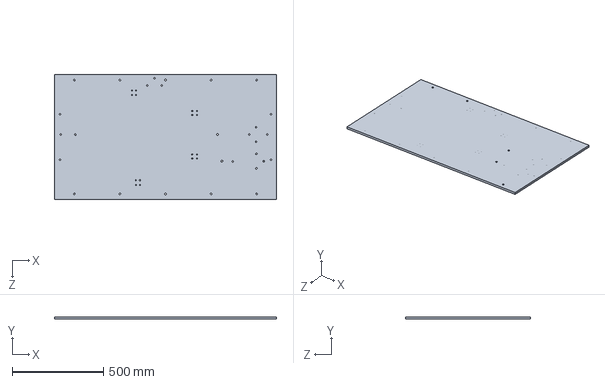
[picture p109: CAD file, 2026-01-19]
01 - Mechanical/CAD/V4 Release 1/Final1masterBase1.SLDPRT
1219.2 x 12.7 x 685.8 mm
