henryhsun/TuxTester/01 - Mechanical/CAD/V4 Release 1/Final1Final145degreeBracket.SLDPRT

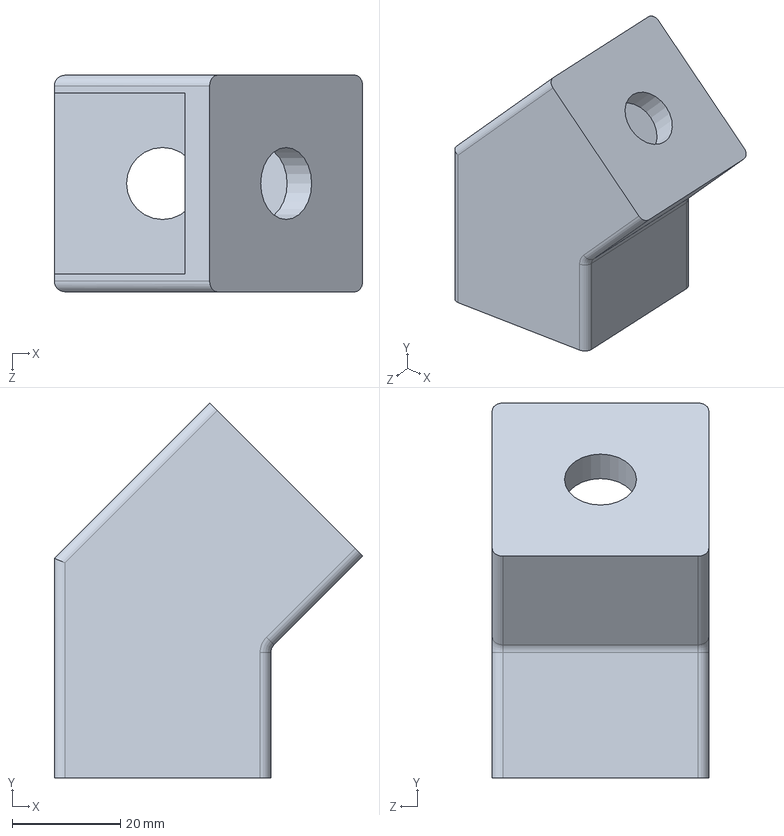
[picture p110: CAD file, 2026-01-19]
01 - Mechanical/CAD/V4 Release 1/Final1Final145degreeBracket.SLDPRT
57.0 x 69.3 x 40.0 mm
