henryhsun/TuxTester/01 - Mechanical/CAD/V4 Release 1/Final1masterCover.SLDPRT

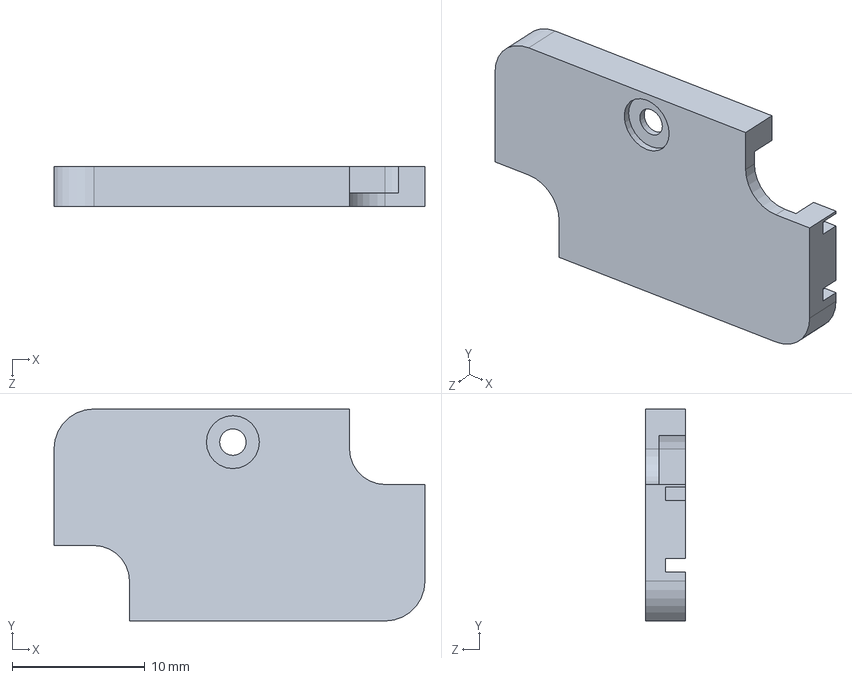
[picture p111: CAD file, 2026-01-19]
01 - Mechanical/CAD/V4 Release 1/Final1masterCover.SLDPRT
28.0 x 16.0 x 3.00 mm
