henryhsun/TuxTester/01 - Mechanical/CAD/V4 Release 1/Final1masterFoot_SheetBase.SLDPRT

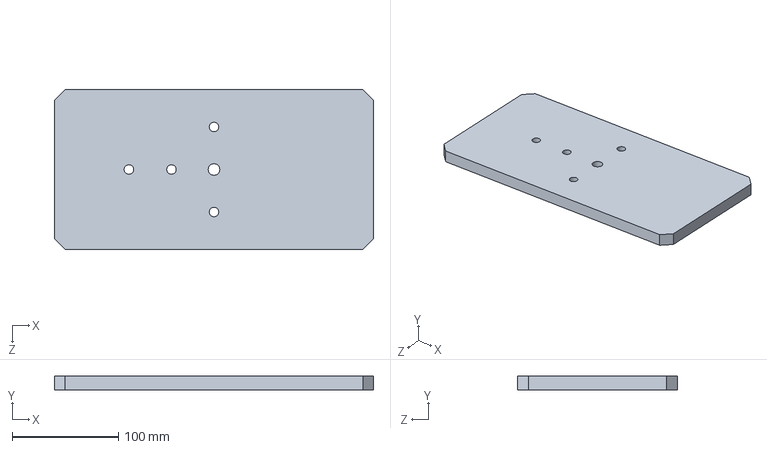
[picture p112: CAD file, 2026-01-19]
01 - Mechanical/CAD/V4 Release 1/Final1masterFoot_SheetBase.SLDPRT
300.0 x 12.7 x 150.0 mm
