henryhsun/TuxTester/01 - Mechanical/CAD/V4 Release 1/Final1master4040_3HoleBracket.SLDPRT

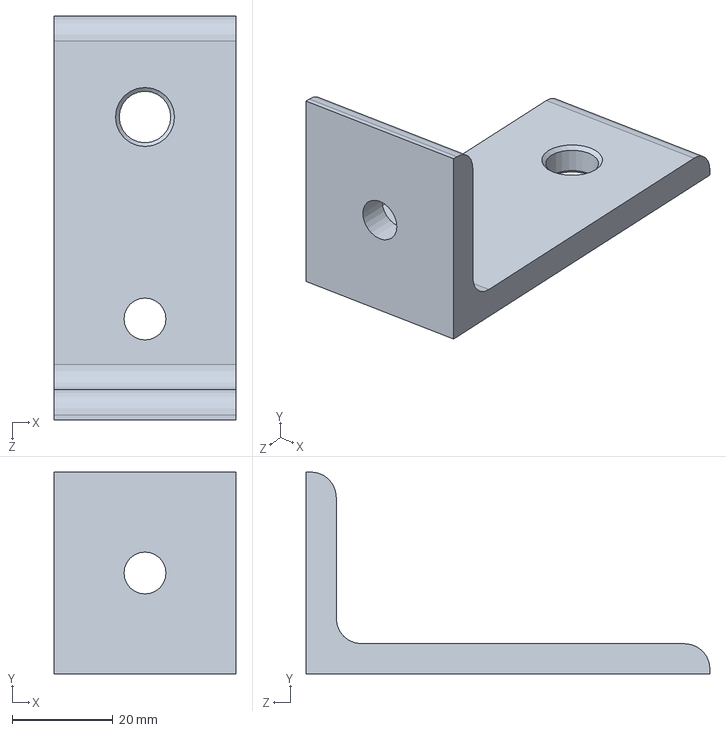
[picture p113: CAD file, 2026-01-19]
01 - Mechanical/CAD/V4 Release 1/Final1master4040_3HoleBracket.SLDPRT
36.0 x 40.0 x 80.0 mm
