henryhsun/TuxTester/01 - Mechanical/CAD/V4 Release 1/Final1masterConnector - straight.SLDPRT

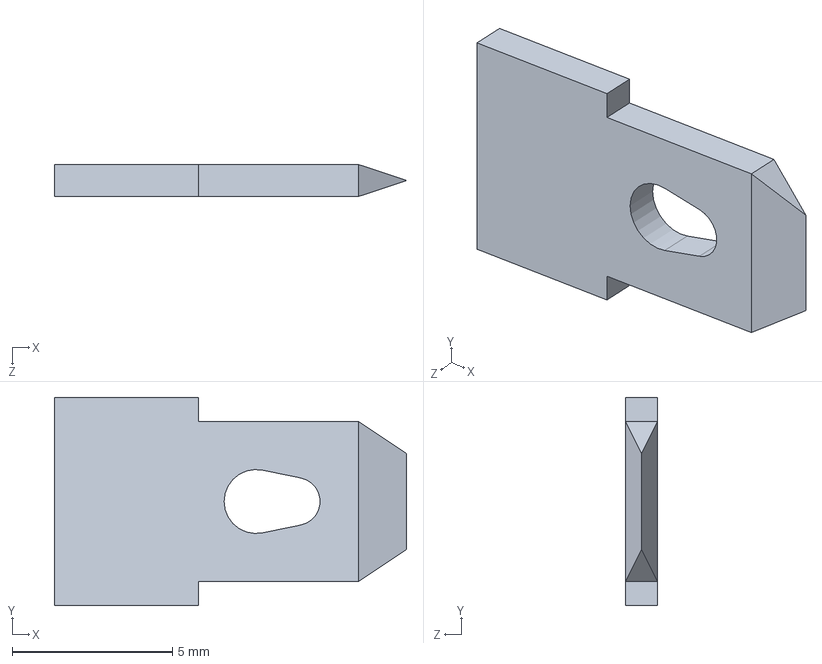
[picture p114: CAD file, 2026-01-19]
01 - Mechanical/CAD/V4 Release 1/Final1masterConnector - straight.SLDPRT
11.0 x 6.50 x 1.00 mm
