henryhsun/TuxTester/01 - Mechanical/CAD/V4 Release 1/Final1master4040 x 130.SLDPRT

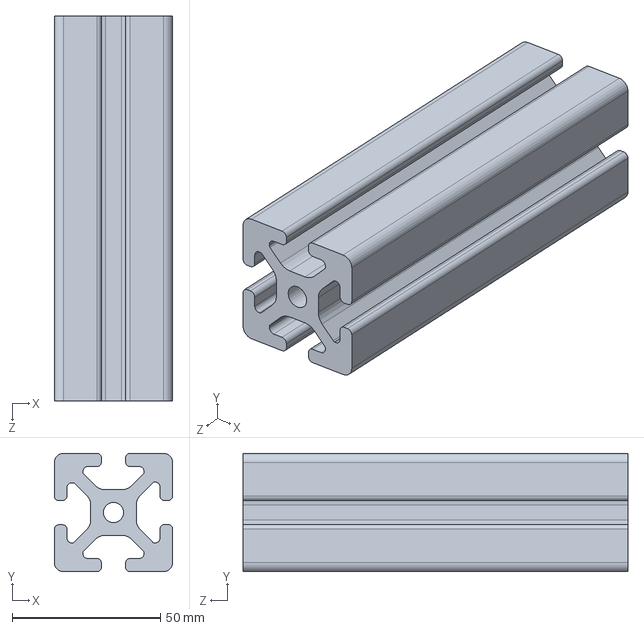
[picture p115: CAD file, 2026-01-19]
01 - Mechanical/CAD/V4 Release 1/Final1master4040 x 130.SLDPRT
40.0 x 40.0 x 130.0 mm
