henryhsun/TuxTester/01 - Mechanical/CAD/V4 Release 1/Final1masterPlate.SLDPRT

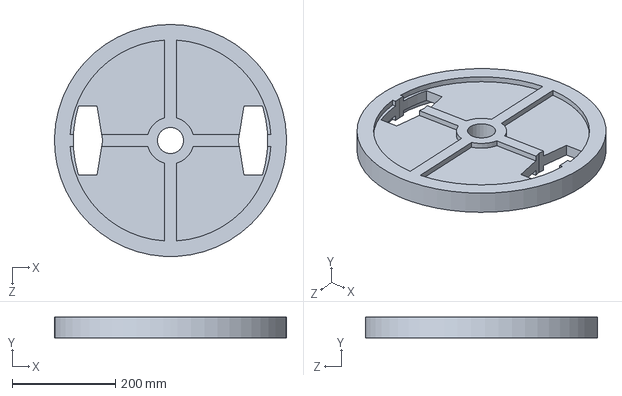
[picture p116: CAD file, 2026-01-19]
01 - Mechanical/CAD/V4 Release 1/Final1masterPlate.SLDPRT
449.8 x 40.0 x 450.0 mm
