henryhsun/TuxTester/01 - Mechanical/CAD/V4 Release 1/OD8025.stp

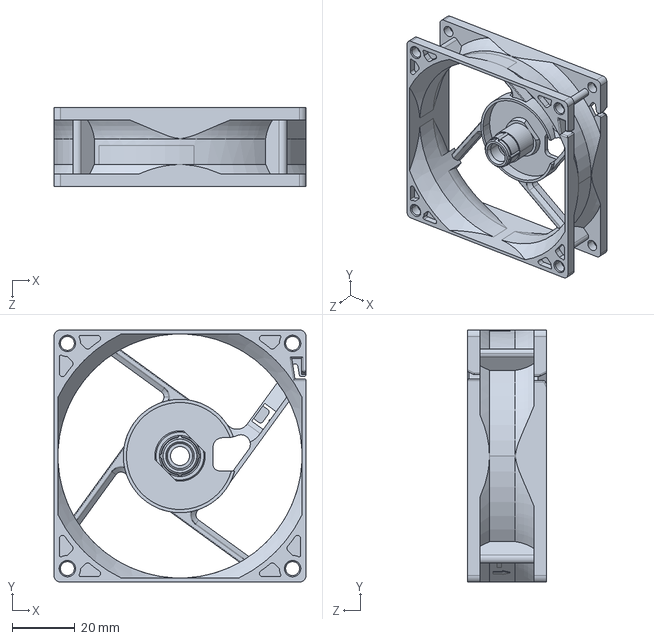
[picture p117: CAD file, 2025-09-29]
01 - Mechanical/CAD/V4 Release 1/OD8025.stp
80.0 x 80.0 x 25.0 mm
