henryhsun/TuxTester/04 - Media/Photos & Videos/02 - Progress Documentation/linear_debug (4).JPG

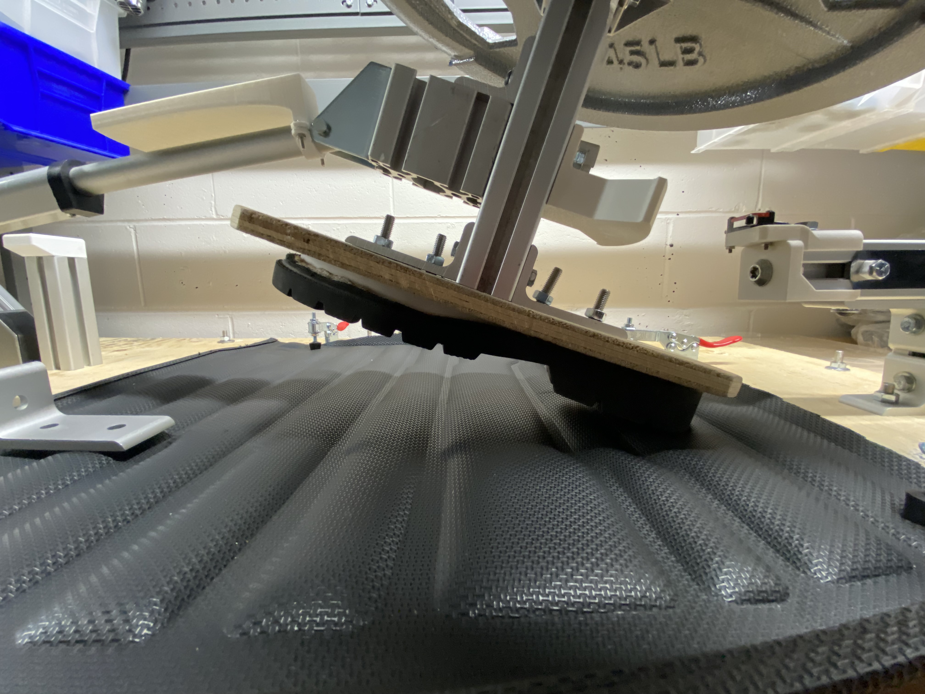
04 - Media/Photos & Videos/02 - Progress Documentation/linear_debug (4).JPG
