henryhsun/TuxTester/04 - Media/Photos & Videos/02 - Progress Documentation/linear_debug (5).JPG

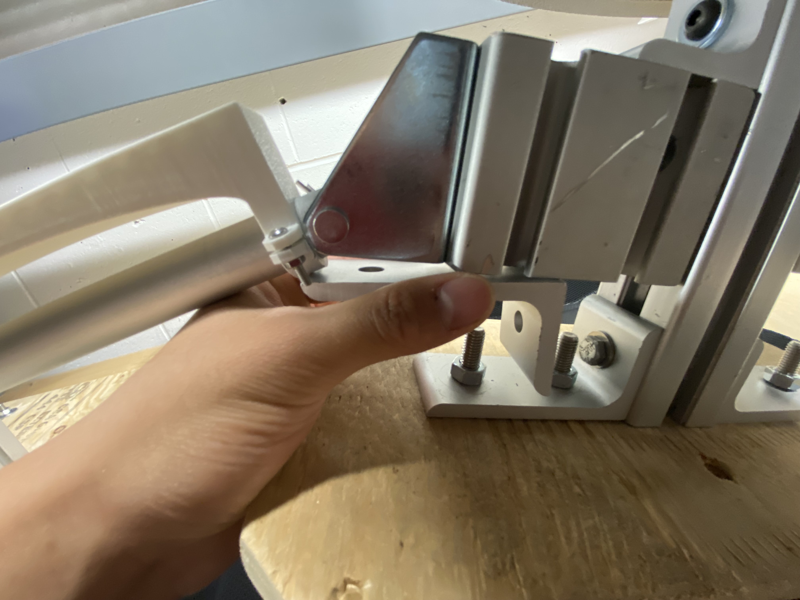
04 - Media/Photos & Videos/02 - Progress Documentation/linear_debug (5).JPG
