henryhsun/TuxTester/04 - Media/Design Sketches/FBD_calculations.jpeg

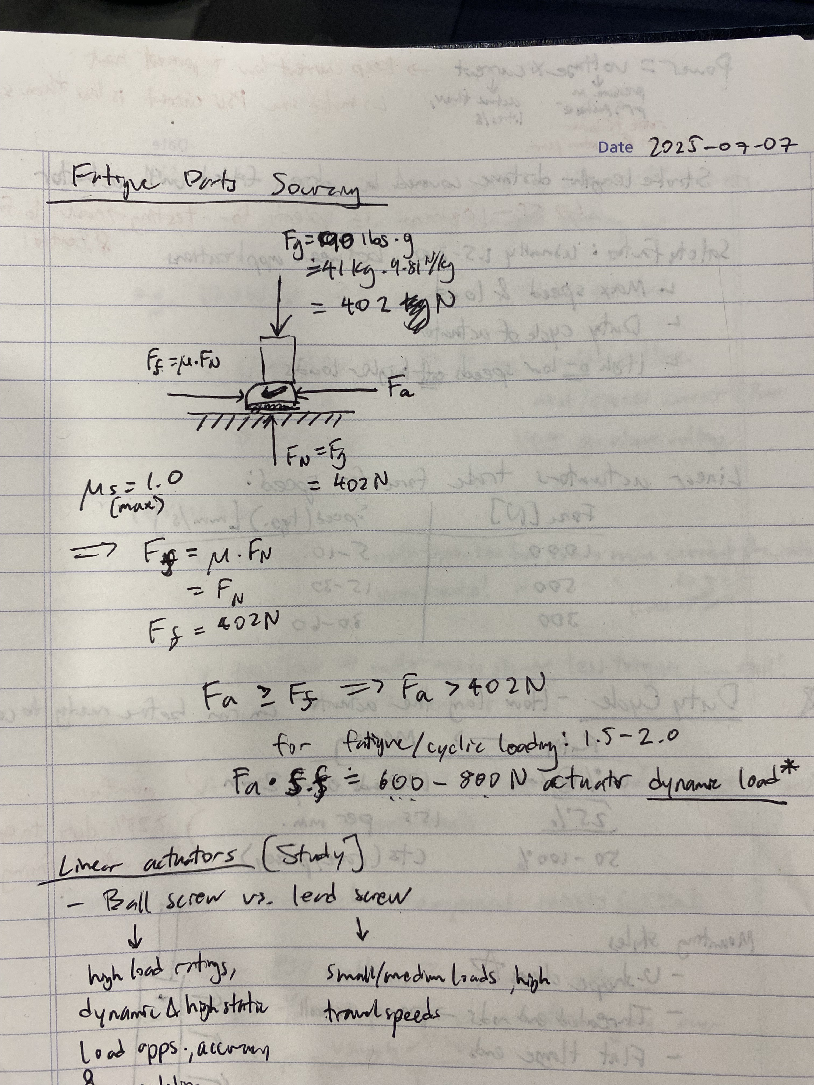
04 - Media/Design Sketches/FBD_calculations.jpeg
