henryhsun/TuxTester/04 - Media/Design Sketches/gantry_concept.jpeg

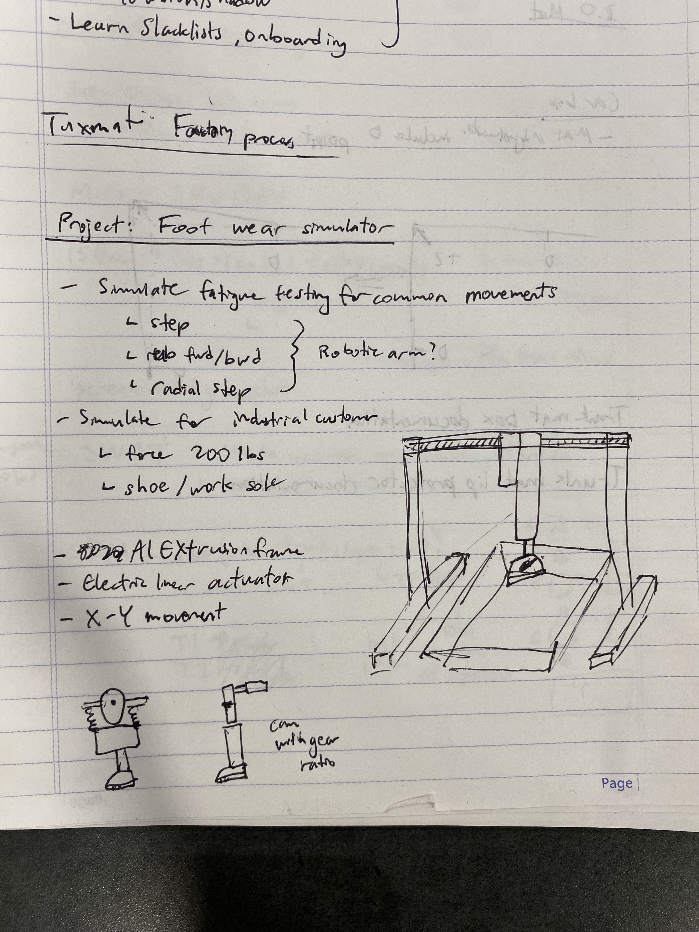
04 - Media/Design Sketches/gantry_concept.jpeg
