henryhsun/TuxTester/04 - Media/Design Sketches/lactuator_concept (1).jpeg

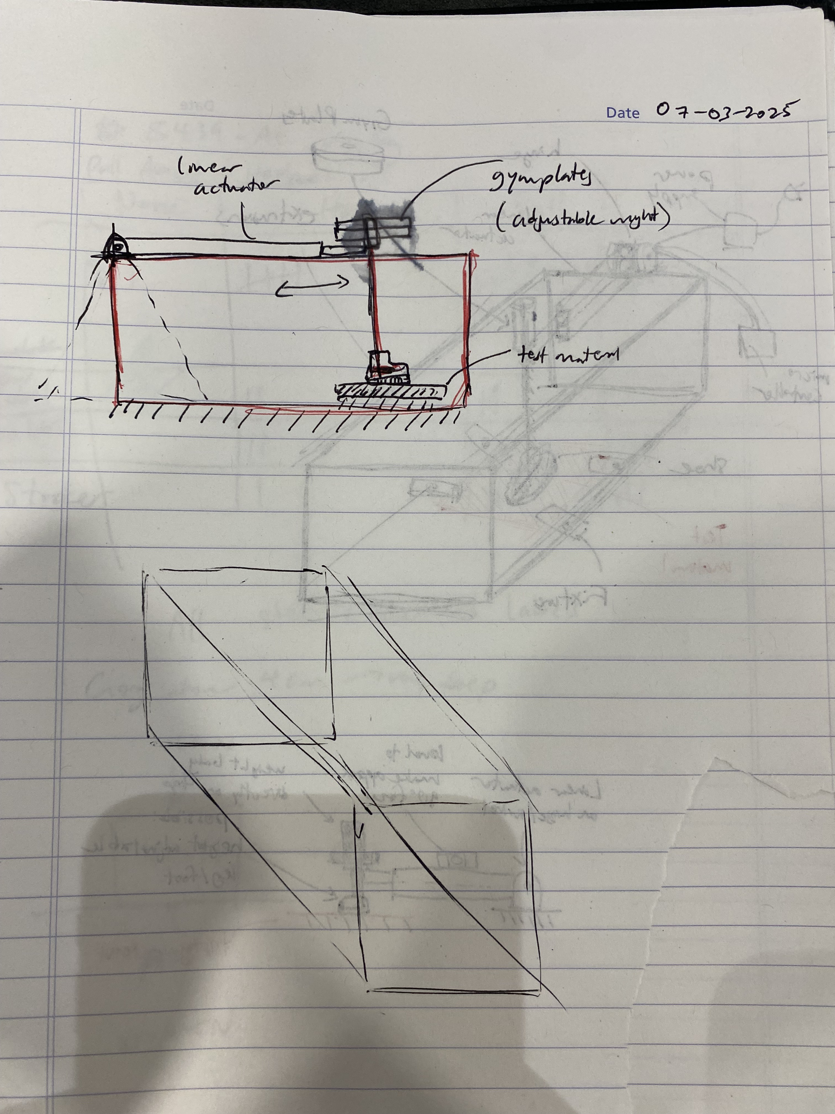
04 - Media/Design Sketches/lactuator_concept (1).jpeg
