henryhsun/TuxTester/04 - Media/Design Sketches/lactuator_concept (2).jpeg

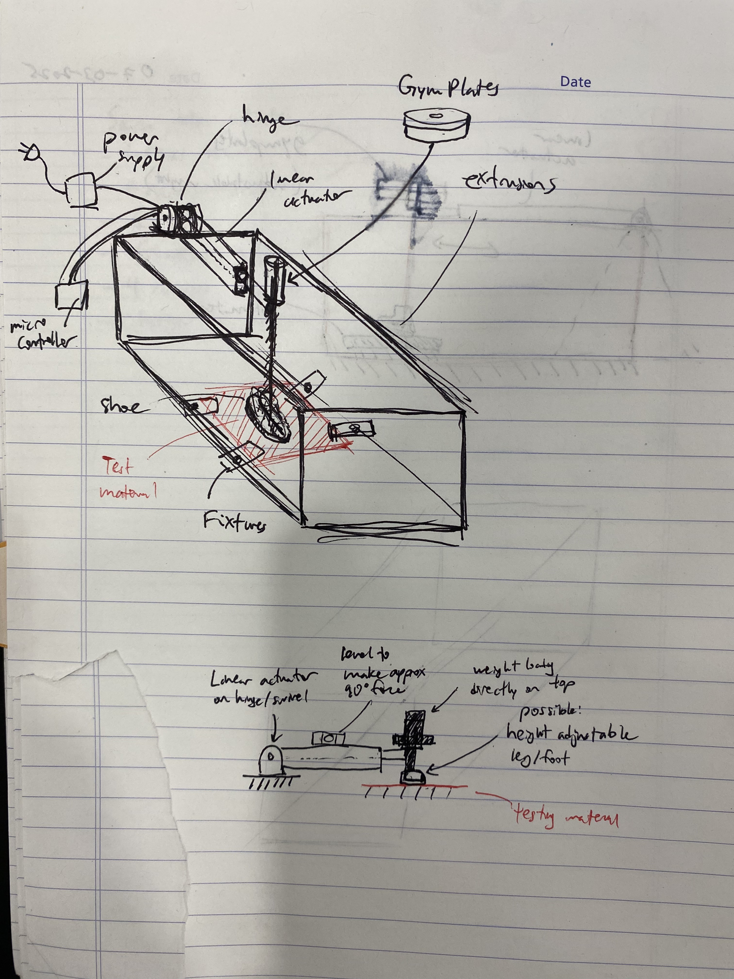
04 - Media/Design Sketches/lactuator_concept (2).jpeg
