henryhsun/TuxTester/04 - Media/Design Sketches/lactuator_concept (3).jpeg

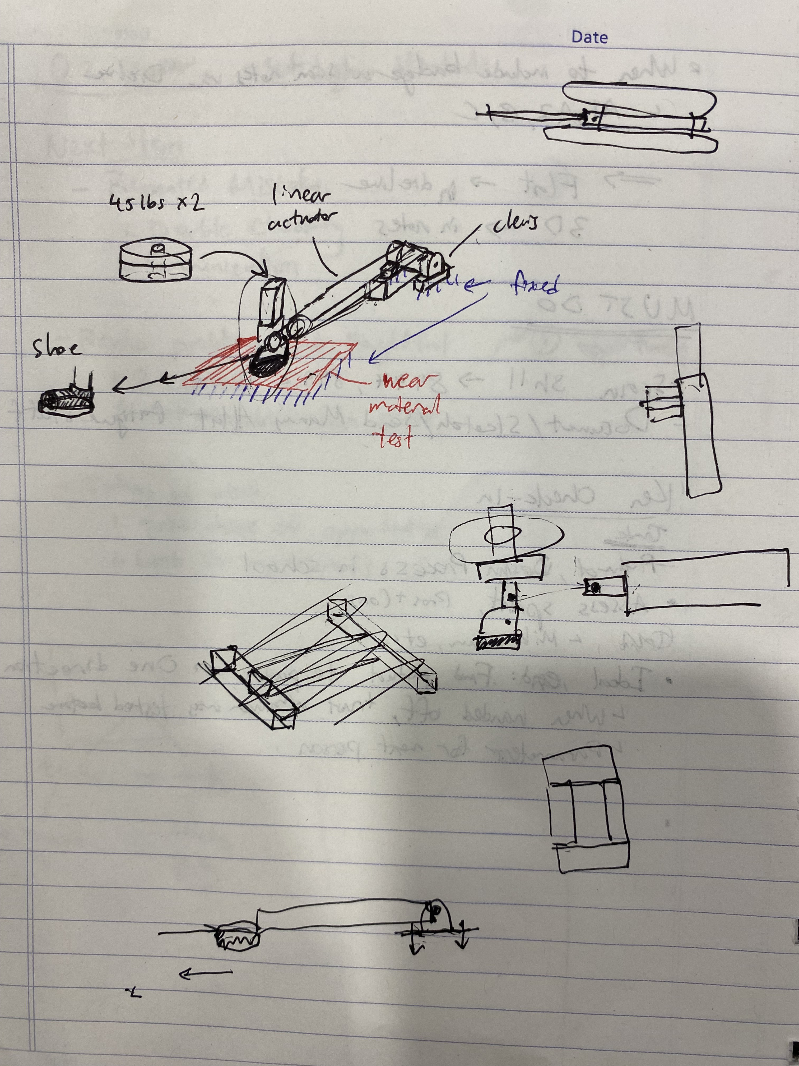
04 - Media/Design Sketches/lactuator_concept (3).jpeg
