henryhsun/TuxTester/04 - Media/Design Sketches/lactuator_draft (1).jpeg

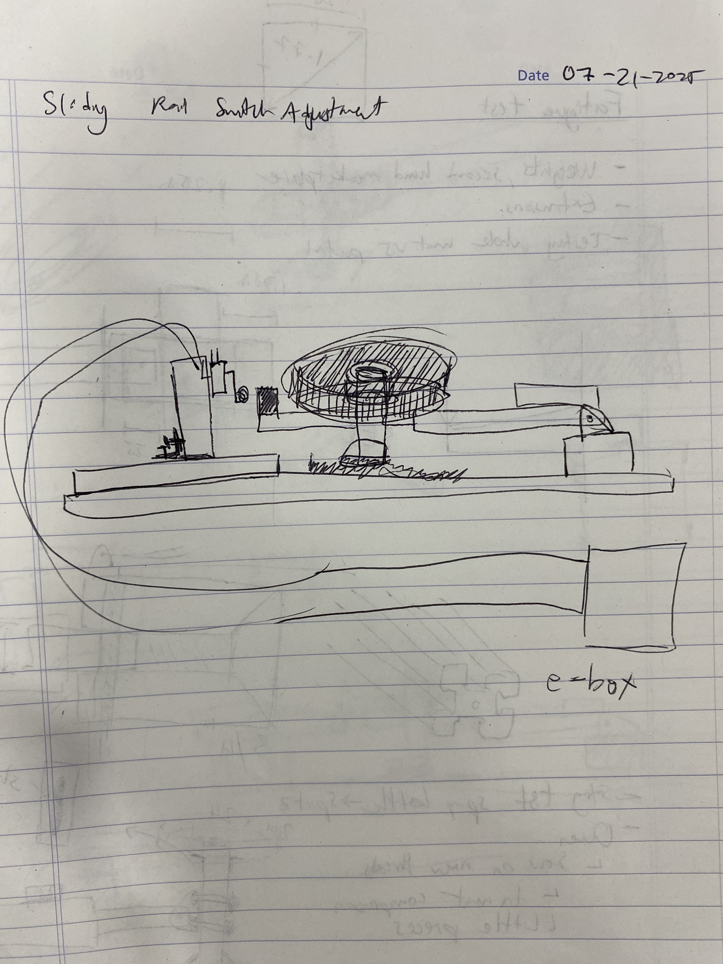
04 - Media/Design Sketches/lactuator_draft (1).jpeg
