henryhsun/TuxTester/04 - Media/Design Sketches/limit_switch (1).jpeg

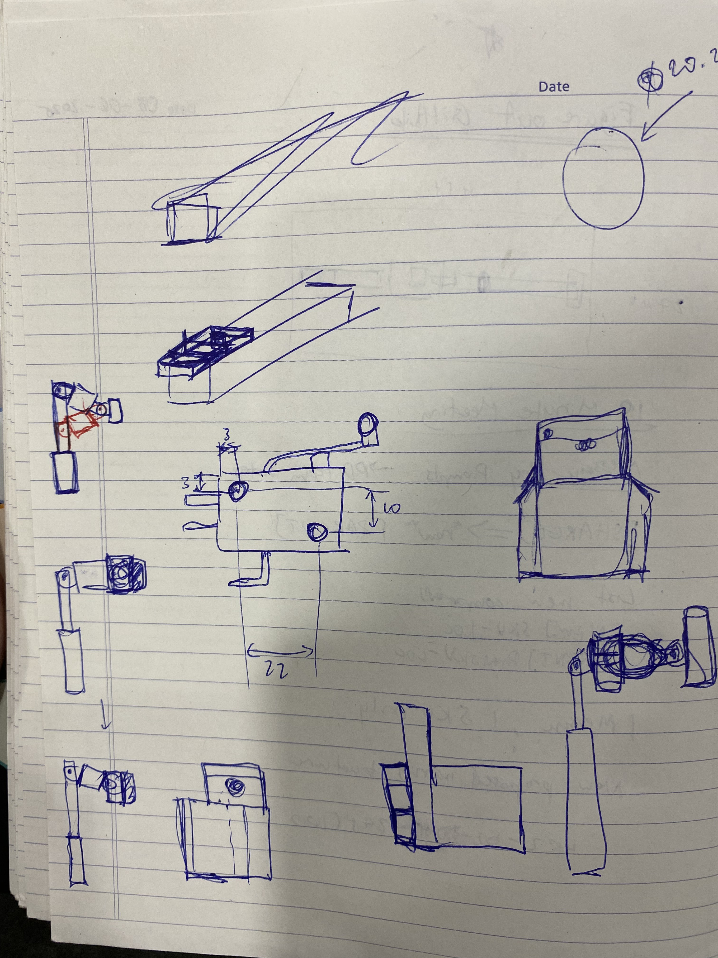
04 - Media/Design Sketches/limit_switch (1).jpeg
