henryhsun/TuxTester/04 - Media/Design Sketches/pulley_concept (2).jpeg

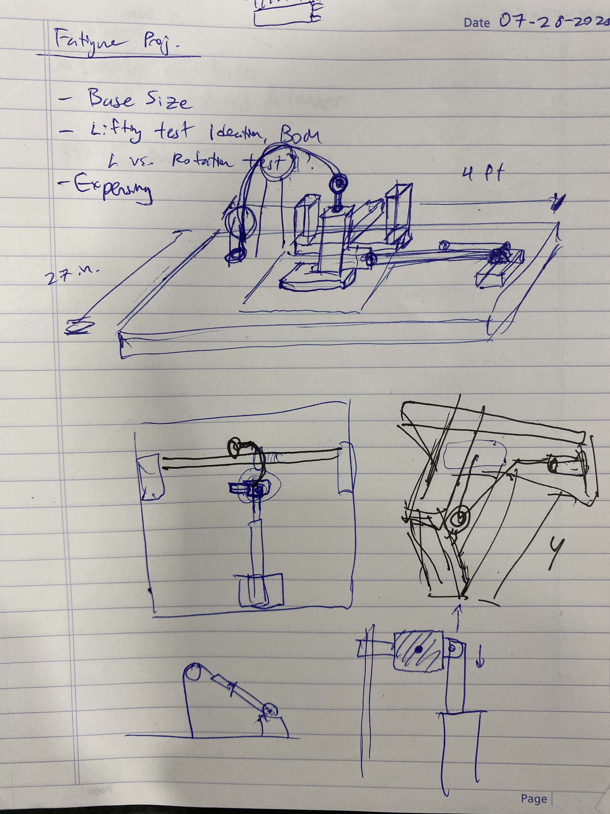
04 - Media/Design Sketches/pulley_concept (2).jpeg
