henryhsun/TuxTester/04 - Media/Design Sketches/rotation_concept (1).jpeg

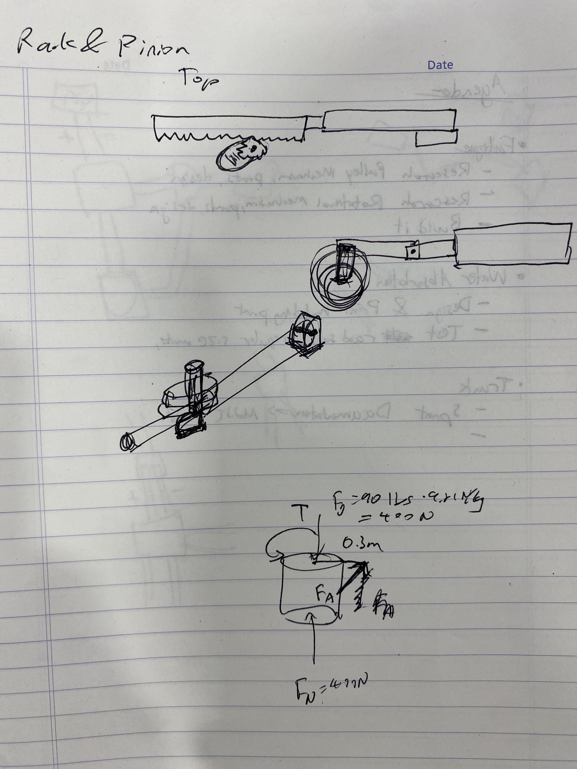
04 - Media/Design Sketches/rotation_concept (1).jpeg
