henryhsun/TuxTester/04 - Media/Photos & Videos/02 - Progress Documentation/IP_electrical (2).JPG

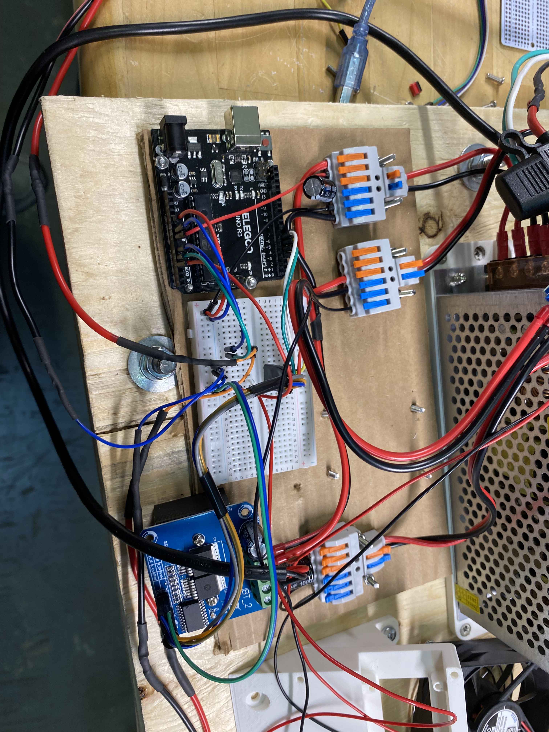
04 - Media/Photos & Videos/02 - Progress Documentation/IP_electrical (2).JPG
